AnMe3z/quadruped-version-3/encoder/encoder-wheels/encoder-wheel.FCStd

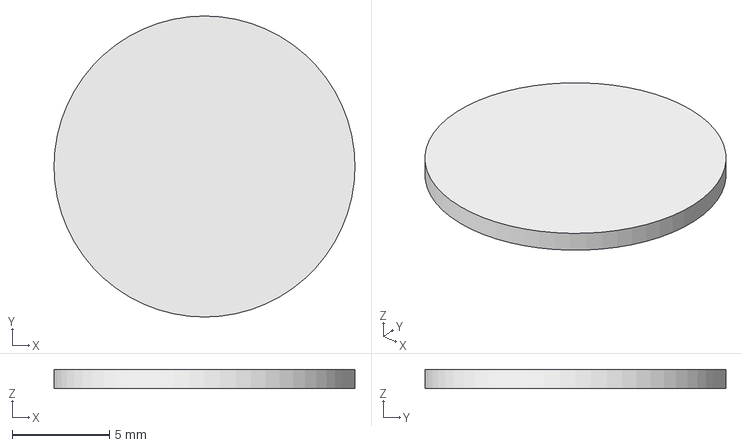
[picture p12: CAD file, 2023-12-13]
encoder/encoder-wheels/encoder-wheel.FCStd
15.5 x 15.5 x 1.00 mm
