AnMe3z/quadruped-version-3/encoder/gears/encoder-gear-Body.stl

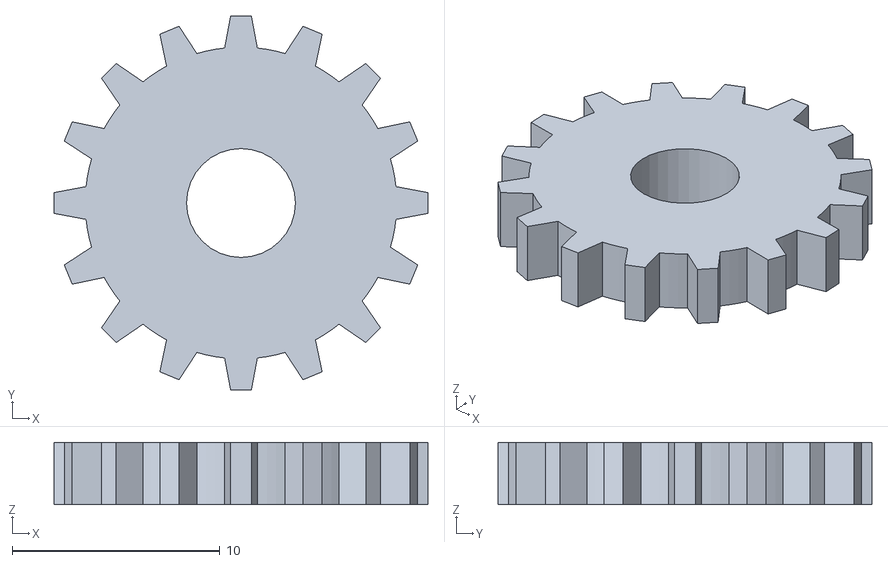
[picture p13: CAD file, 2023-12-22]
encoder/gears/encoder-gear-Body.stl
18.0 x 18.0 x 3.00
