AnMe3z/quadruped-version-3/encoder/sensor-base.FCStd

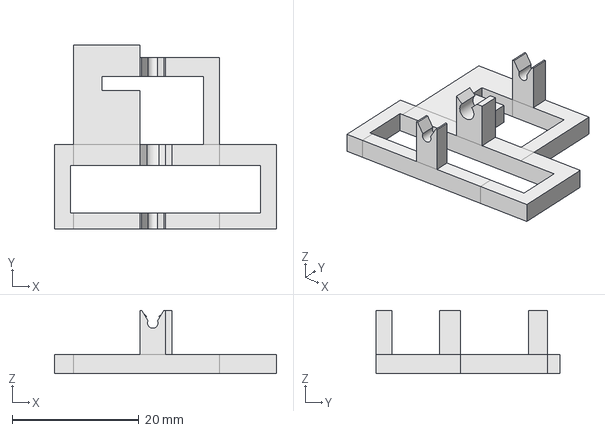
[picture p14: CAD file, 2023-12-06]
encoder/sensor-base.FCStd
35.0 x 29.0 x 10.0 mm
