AnMe3z/quadruped-version-3/encoder/wingEncoder/wing.FCStd

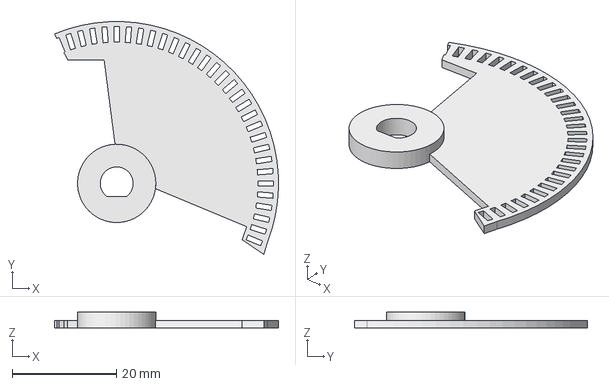
[picture p15: CAD file, 2023-12-23]
encoder/wingEncoder/wing.FCStd
42.9 x 44.6 x 3.00 mm
