AnMe3z/quadruped-version-3/hardware/body/parallel.FCStd

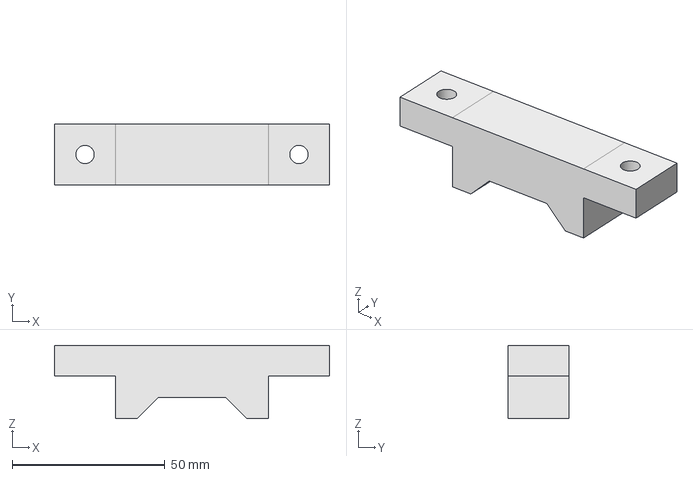
[picture p16: CAD file, 2024-03-18]
hardware/body/parallel.FCStd
90.0 x 20.0 x 24.0 mm
