AnMe3z/quadruped-version-3/hardware/leg/femur/femur-fragmented/femur-left.FCStd

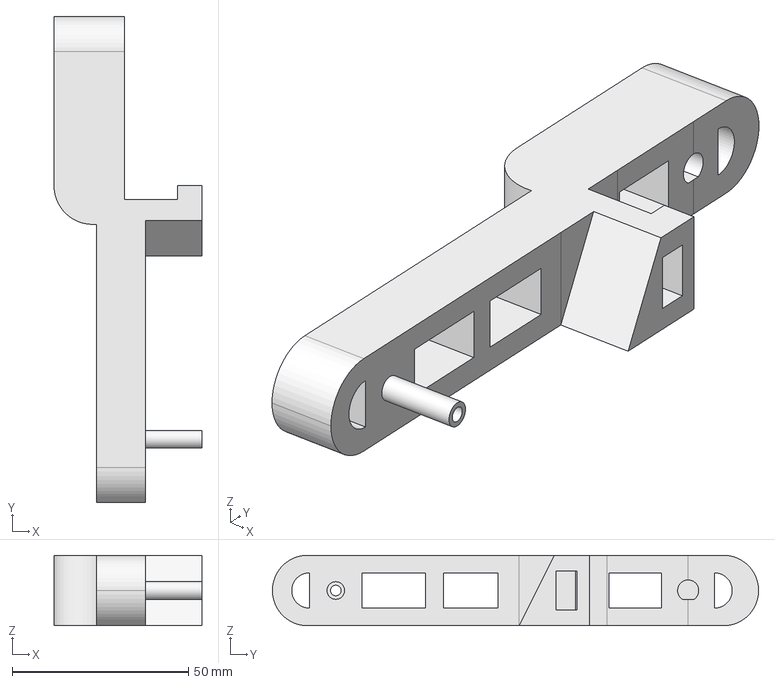
[picture p17: CAD file, 2023-12-28]
hardware/leg/femur/femur-fragmented/femur-left.FCStd
42.0 x 138.0 x 20.0 mm
