AnMe3z/quadruped-version-3/hardware/leg/femur/femur-inner.FCStd

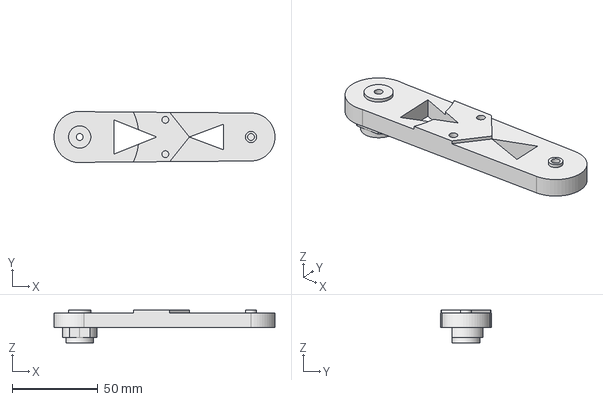
[picture p18: CAD file, 2024-04-03]
hardware/leg/femur/femur-inner.FCStd
129.0 x 30.0 x 19.0 mm
