AnMe3z/quadruped-version-3/hardware/leg/femur/tensioners/btens14.stl

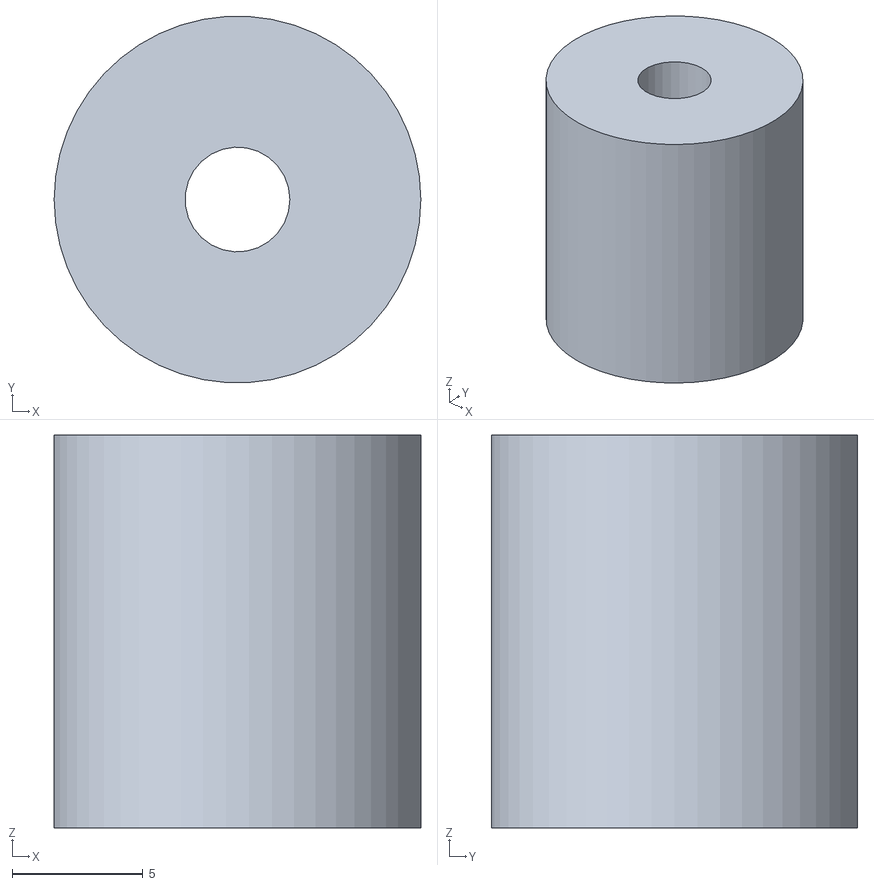
[picture p19: CAD file, 2024-01-30]
hardware/leg/femur/tensioners/btens14.stl
14.0 x 14.0 x 15.0
