AnMe3z/quadruped-version-3/hardware/leg/gears/Pulley_GT2-2MM-40T-11SH.stl

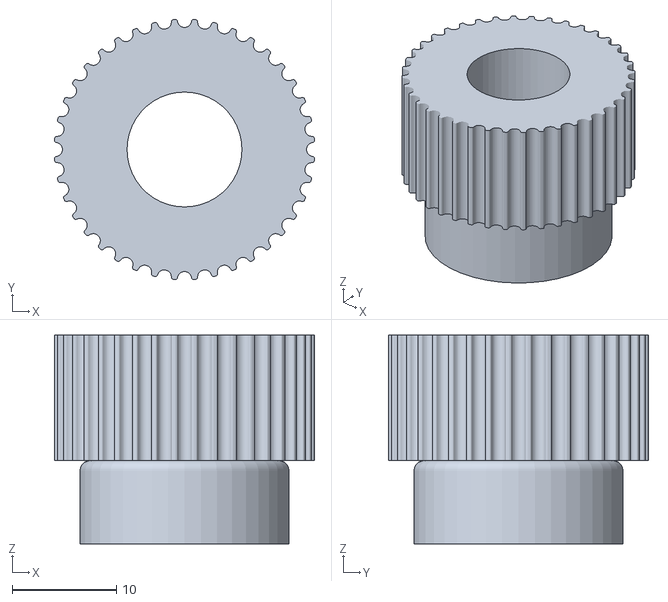
[picture p20: CAD file, 2024-02-03]
hardware/leg/gears/Pulley_GT2-2MM-40T-11SH.stl
24.9 x 24.9 x 20.0
