AnMe3z/quadruped-version-3/hardware/leg/hip/hip-lower/hip-lower-BR.stl

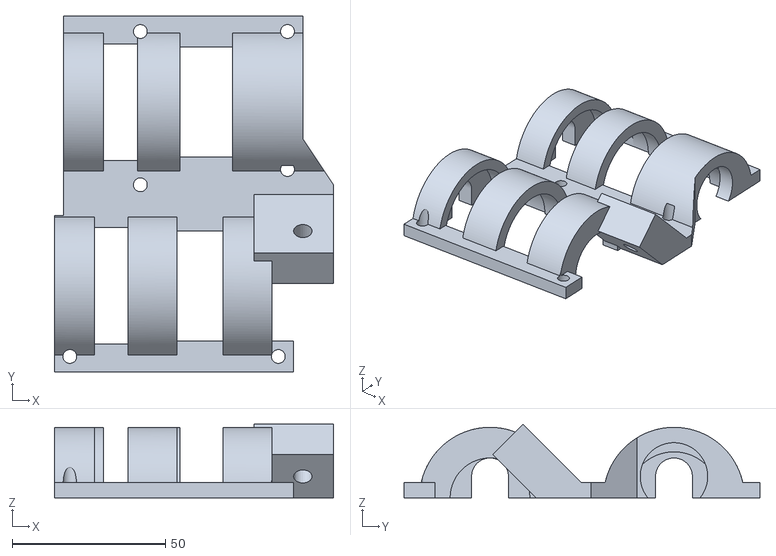
[picture p21: CAD file, 2024-02-26]
hardware/leg/hip/hip-lower/hip-lower-BR.stl
91.0 x 116.0 x 24.0
