AnMe3z/quadruped-version-3/hardware/leg/hip/hip-sensor-cap/hip-encoder-shell-long-proper-mirror.stl

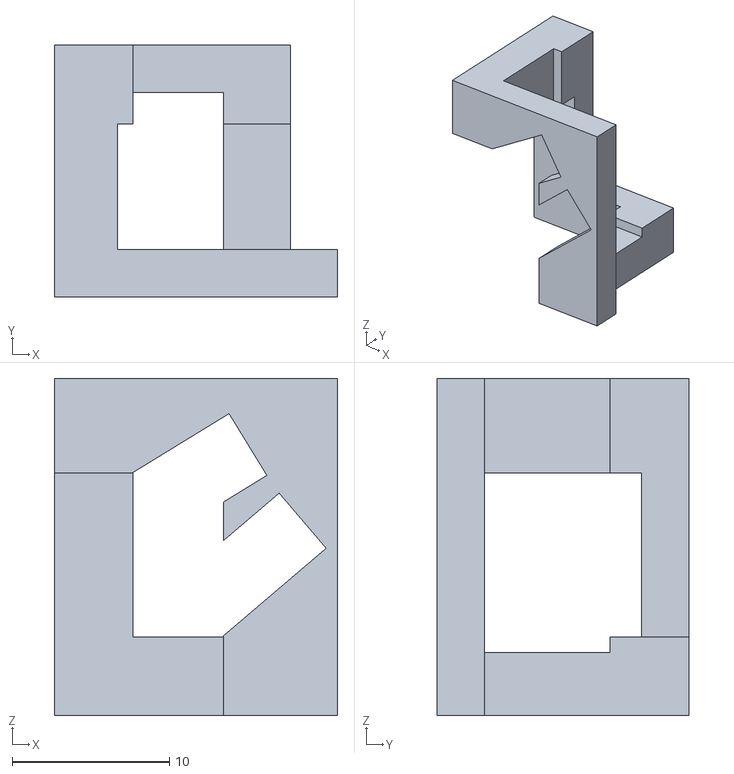
[picture p22: CAD file, 2024-04-03]
hardware/leg/hip/hip-sensor-cap/hip-encoder-shell-long-proper-mirror.stl
18.0 x 16.0 x 21.4
