AnMe3z/quadruped-version-3/hardware/leg/hip/hip-upper/hip-upper-BL.stl

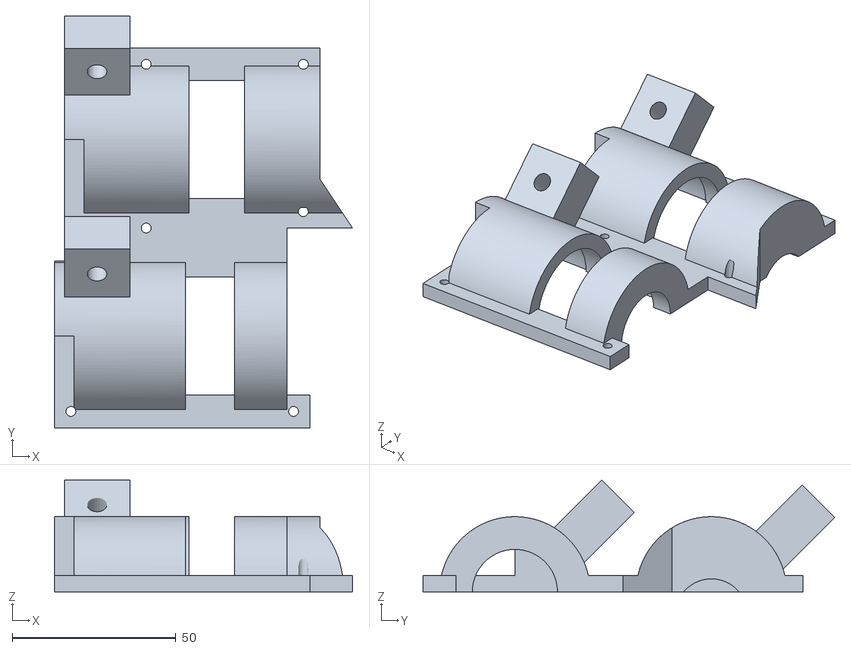
[picture p23: CAD file, 2024-02-26]
hardware/leg/hip/hip-upper/hip-upper-BL.stl
91.0 x 125.7 x 34.2
