AnMe3z/quadruped-version-3/hardware/leg/knee/cuts/61.stl

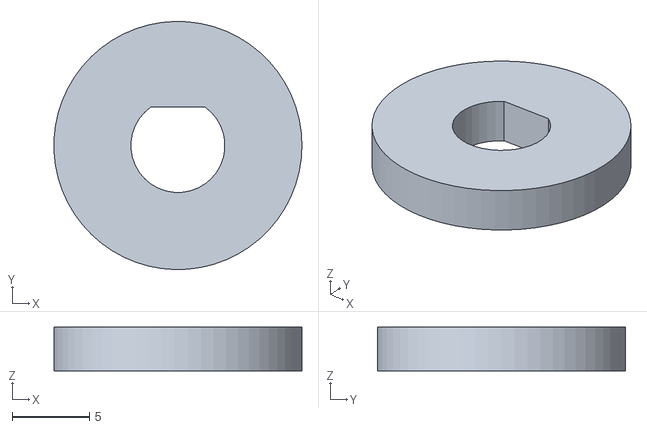
[picture p24: CAD file, 2024-04-03]
hardware/leg/knee/cuts/61.stl
16.1 x 16.1 x 2.83
