AnMe3z/quadruped-version-3/hardware/leg/knee/knee-drive.FCStd

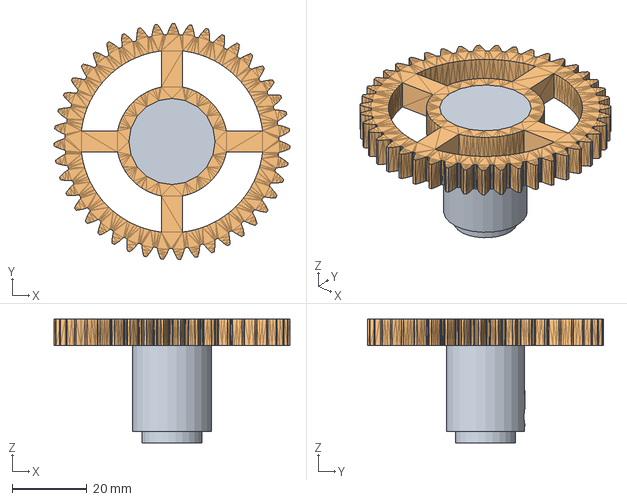
[picture p25: CAD file, 2024-04-03]
hardware/leg/knee/knee-drive.FCStd
63.0 x 63.0 x 33.0 mm
Stunning_Amberis__1_001 (Solid)
