AnMe3z/quadruped-version-3/hardware/leg/knee/knee-fragmented/knee-left.FCStd

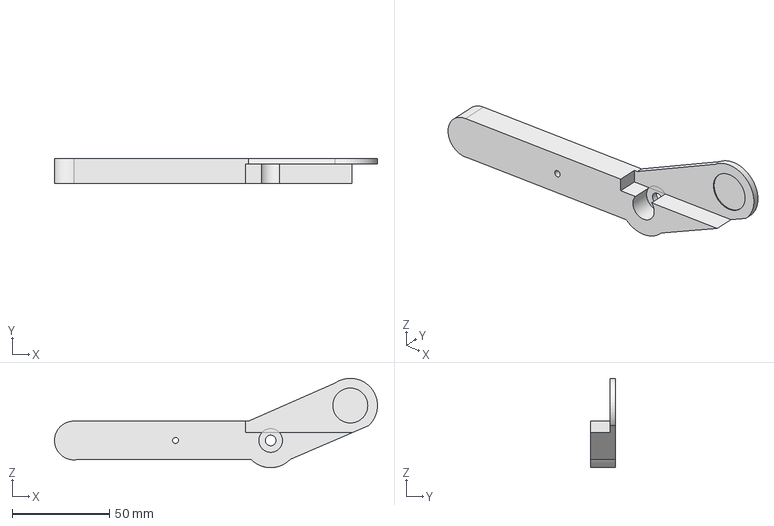
[picture p26: CAD file, 2023-12-28]
hardware/leg/knee/knee-fragmented/knee-left.FCStd
166.3 x 13.0 x 46.0 mm
