AnMe3z/quadruped-version-3/hardware/leg/leg-45.stl

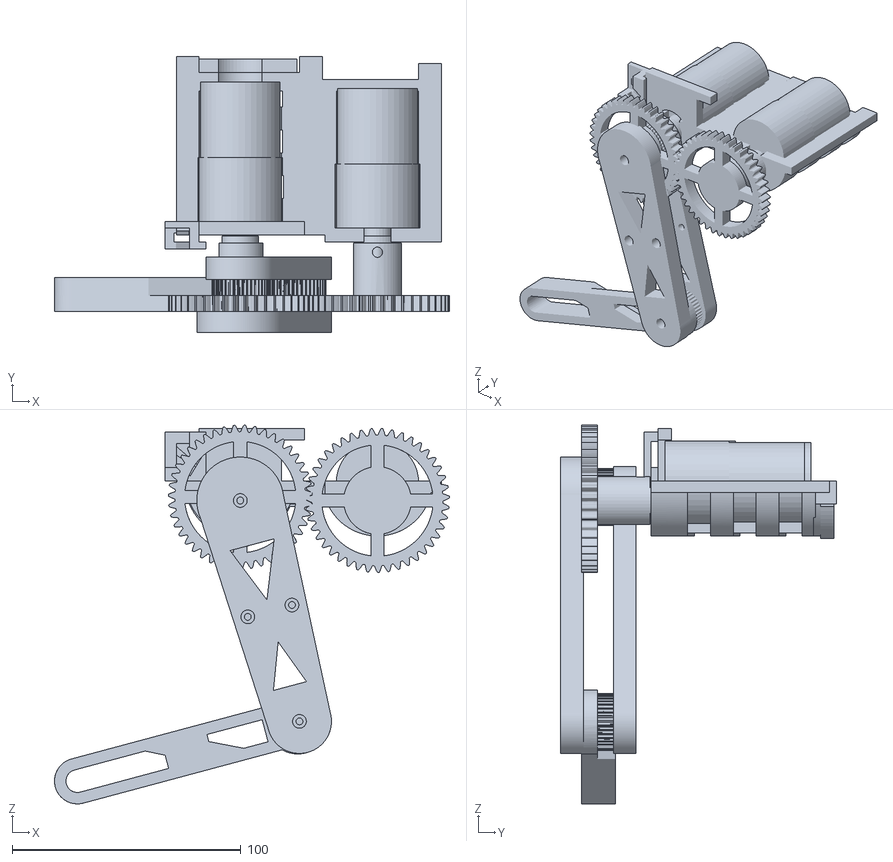
[picture p27: CAD file, 2024-02-03]
hardware/leg/leg-45.stl
172.7 x 120.5 x 165.7
