AnMe3z/quadruped-version-3/hardware/motor/test-fitting.FCStd

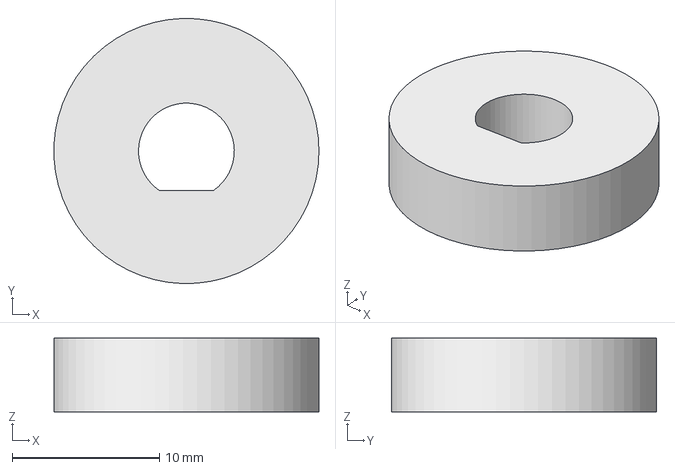
[picture p28: CAD file, 2024-01-26]
hardware/motor/test-fitting.FCStd
18.0 x 18.0 x 5.00 mm
