AnMe3z/quadruped-version-3/hardware/schematics/parts/3d-models/raspberry-pi-pico-w-rp2040-no-pins-pins-and-socketed-1.snapshot.5/RaspberryPi-PicoW-NoPins.step

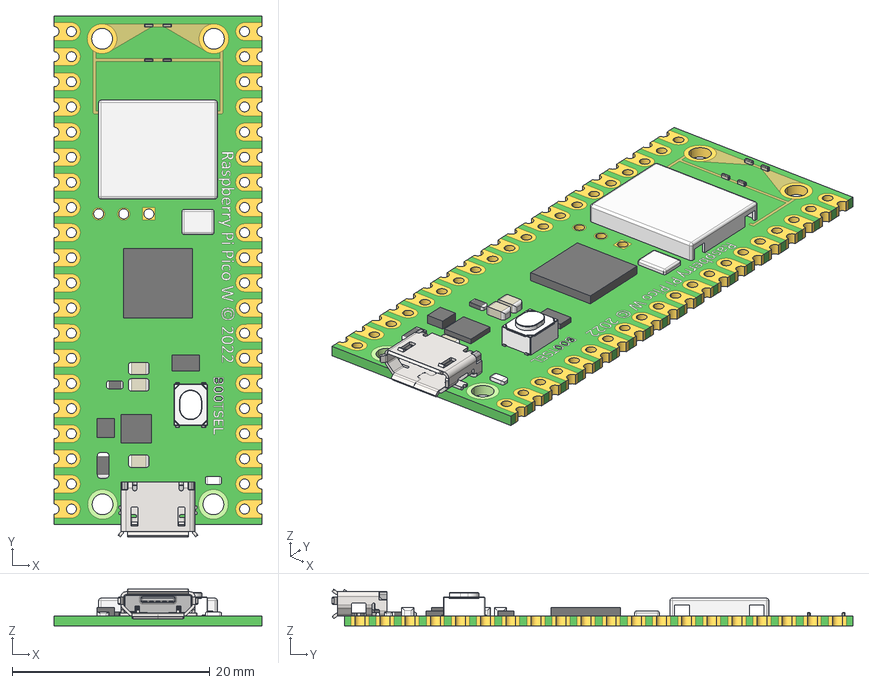
[picture p29: CAD file, 2024-02-05]
hardware/schematics/parts/3d-models/raspberry-pi-pico-w-rp2040-no-pins-pins-and-socketed-1.snapshot.5/RaspberryPi-PicoW-NoPins.step
21.0 x 52.7 x 3.71 mm
