AnMe3z/quadruped-version-3/hip/knee-drive.FCStd

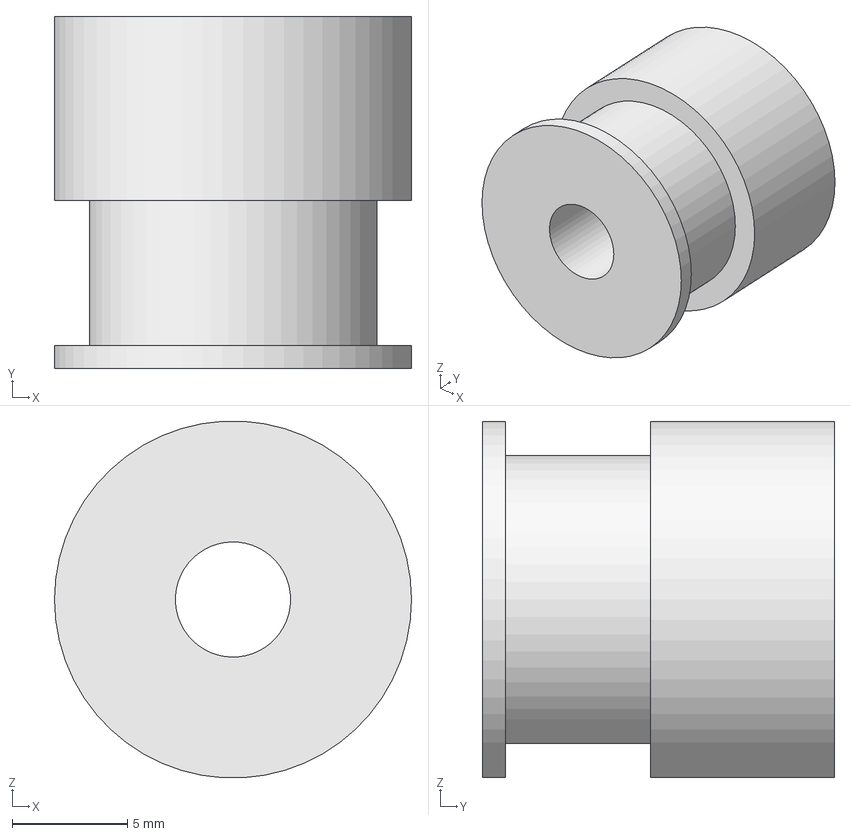
[picture p30: CAD file, 2023-10-18]
hip/knee-drive.FCStd
15.5 x 15.3 x 15.5 mm
