AnMe3z/quadruped-version-3/knee/knee-belt-drive-realistic.FCStd

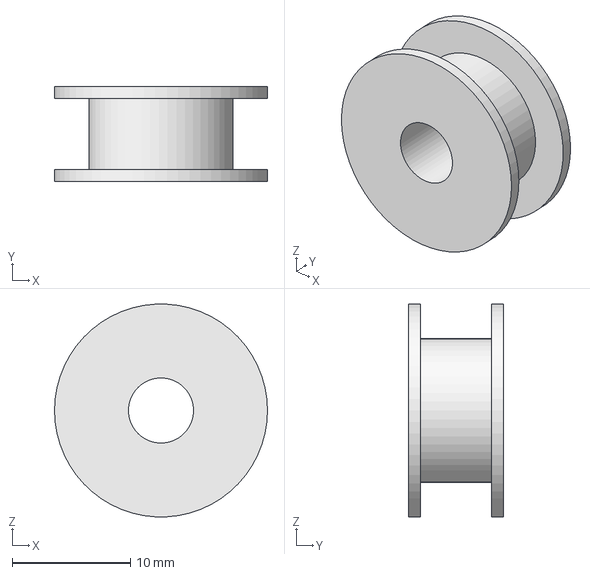
[picture p31: CAD file, 2023-10-26]
knee/knee-belt-drive-realistic.FCStd
18.0 x 8.00 x 18.0 mm
