AnMe3z/quadruped-version-3/encoder/wingEncoder/ledCover.FCStd

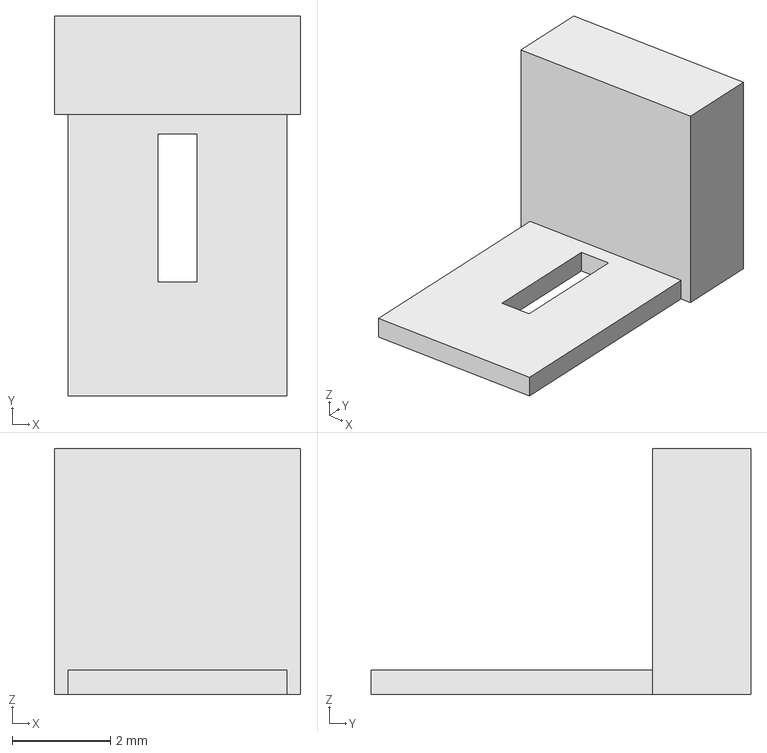
[picture p33: CAD file, 2023-12-22]
encoder/wingEncoder/ledCover.FCStd
5.00 x 7.72 x 5.00 mm
