AnMe3z/quadruped-version-3/hardware/body/side-lower-back.stl

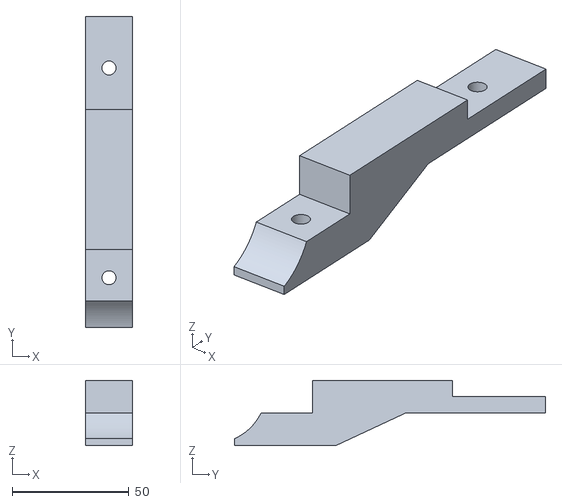
[picture p34: CAD file, 2024-03-18]
hardware/body/side-lower-back.stl
20.0 x 133.4 x 28.0
