AnMe3z/quadruped-version-3/hardware/leg/femur/tensioners/btens10.FCStd

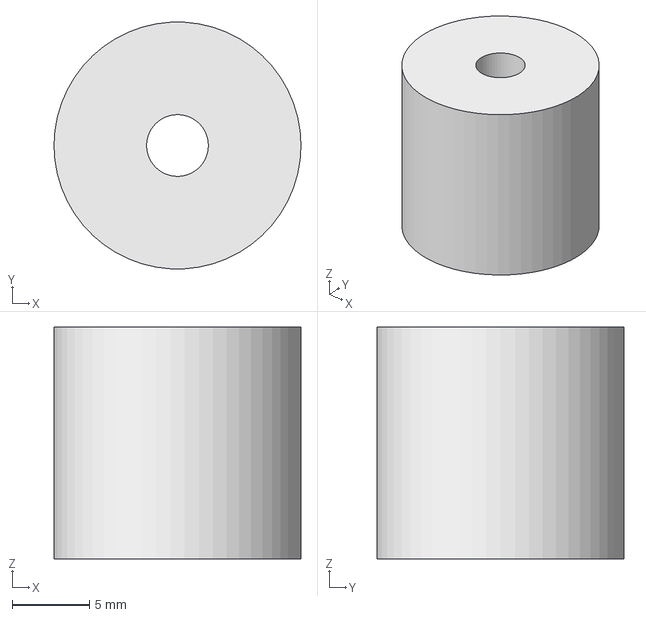
[picture p35: CAD file, 2024-01-30]
hardware/leg/femur/tensioners/btens10.FCStd
16.0 x 16.0 x 15.0 mm
