AnMe3z/quadruped-version-3/hardware/leg/gears/belt-gear.stl

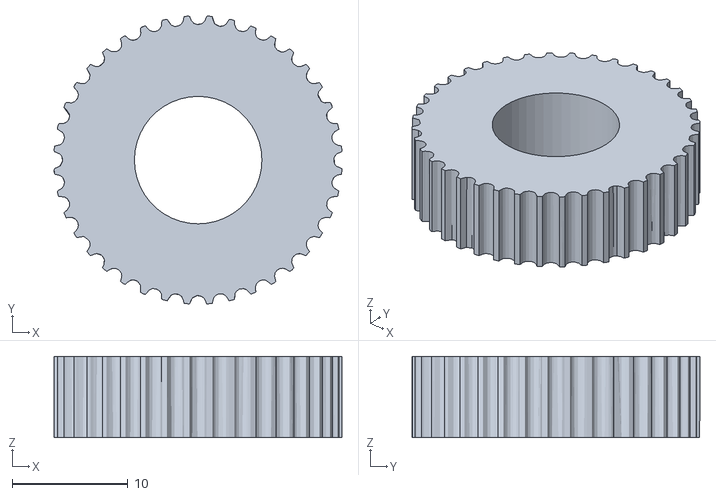
[picture p36: CAD file, 2024-02-03]
hardware/leg/gears/belt-gear.stl
24.9 x 24.8 x 7.00
