AnMe3z/quadruped-version-3/hardware/leg/hip/hip-sensor-cap/hip-sensor-cap.FCStd

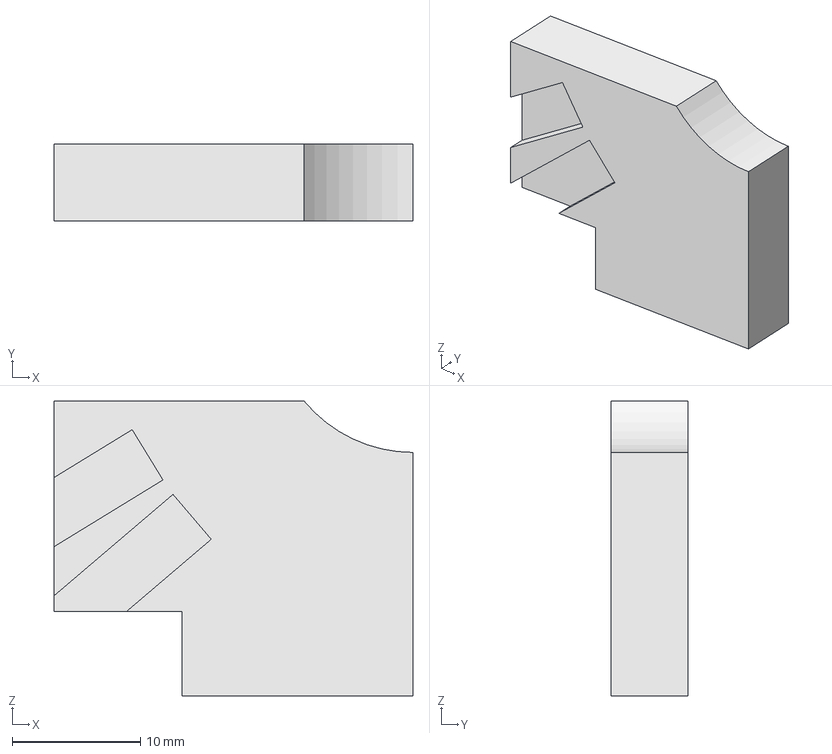
[picture p37: CAD file, 2024-03-18]
hardware/leg/hip/hip-sensor-cap/hip-sensor-cap.FCStd
28.0 x 6.00 x 23.0 mm
