AnMe3z/quadruped-version-3/hardware/leg/knee/knee-fragmented/knee-right.FCStd

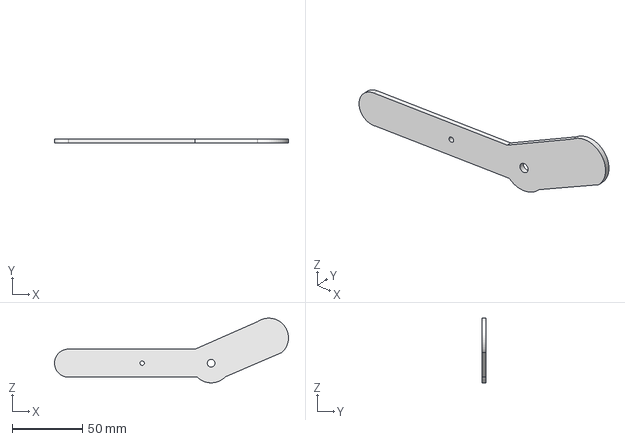
[picture p38: CAD file, 2023-12-28]
hardware/leg/knee/knee-fragmented/knee-right.FCStd
166.3 x 3.00 x 46.0 mm
