AnMe3z/quadruped-version-3/hardware/motor/xd-37gb520.FCStd

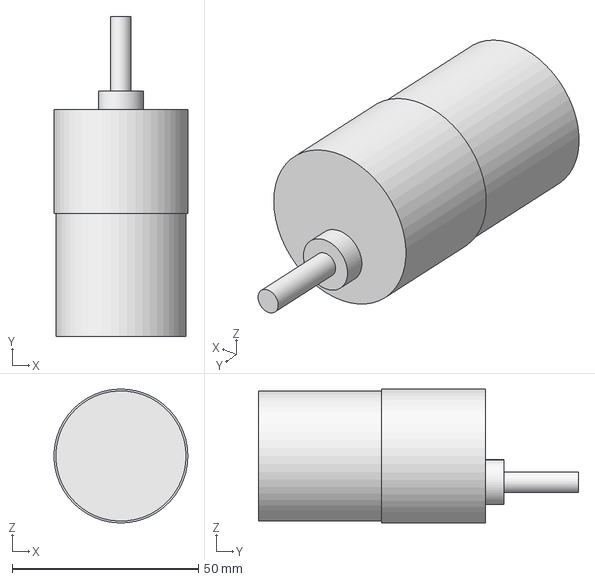
[picture p39: CAD file, 2023-10-10]
hardware/motor/xd-37gb520.FCStd
36.0 x 86.0 x 36.0 mm
