AnMe3z/quadruped-version-3/knee/knee-belt-drive.FCStd

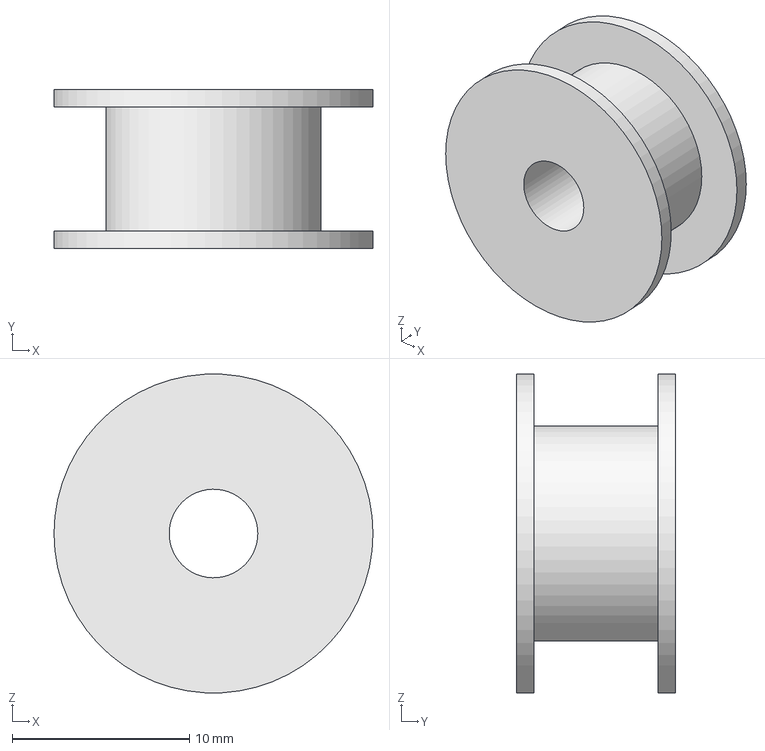
[picture p40: CAD file, 2023-10-18]
knee/knee-belt-drive.FCStd
18.0 x 9.00 x 18.0 mm
