AnMe3z/quadruped-version-3/encoder/gears/middle-gear-Body.stl

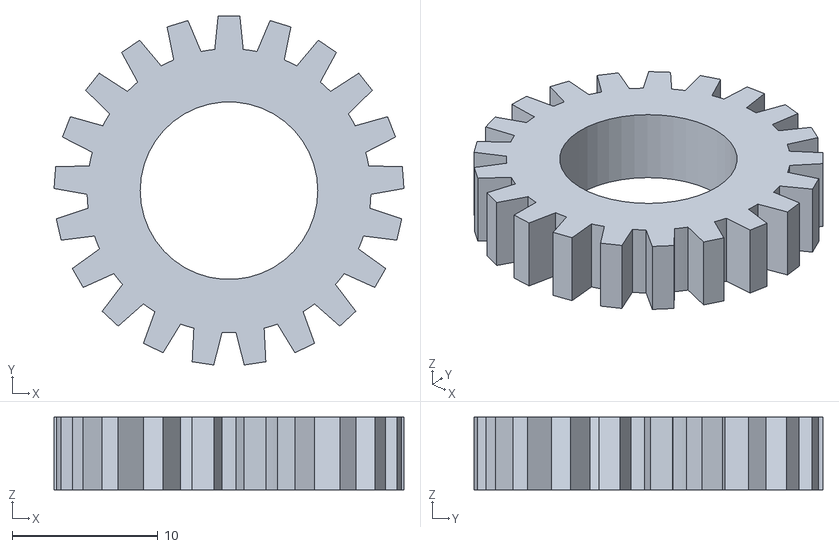
[picture p41: CAD file, 2023-12-17]
encoder/gears/middle-gear-Body.stl
24.0 x 24.0 x 5.00
