AnMe3z/quadruped-version-3/hardware/body/side-lower-front.stl

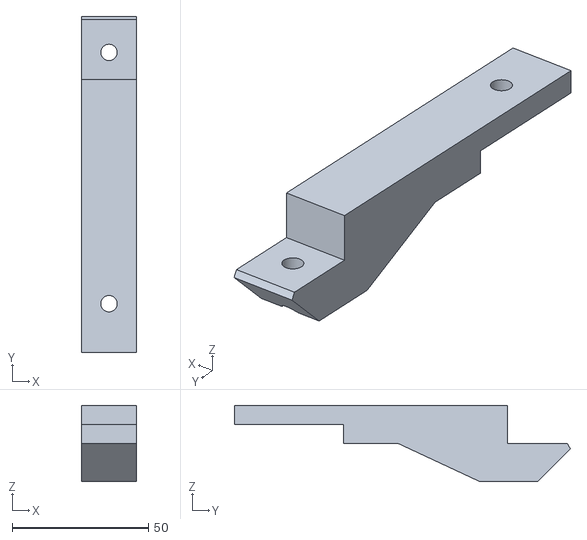
[picture p42: CAD file, 2024-03-18]
hardware/body/side-lower-front.stl
20.0 x 123.2 x 28.0
