AnMe3z/quadruped-version-3/hardware/leg/femur/femur-fragmented/femur-right.FCStd

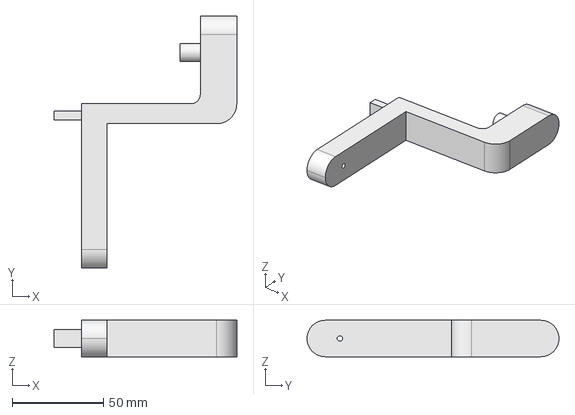
[picture p43: CAD file, 2023-10-26]
hardware/leg/femur/femur-fragmented/femur-right.FCStd
100.0 x 138.0 x 20.0 mm
