AnMe3z/quadruped-version-3/hardware/leg/femur/femur-outer-Body.stl

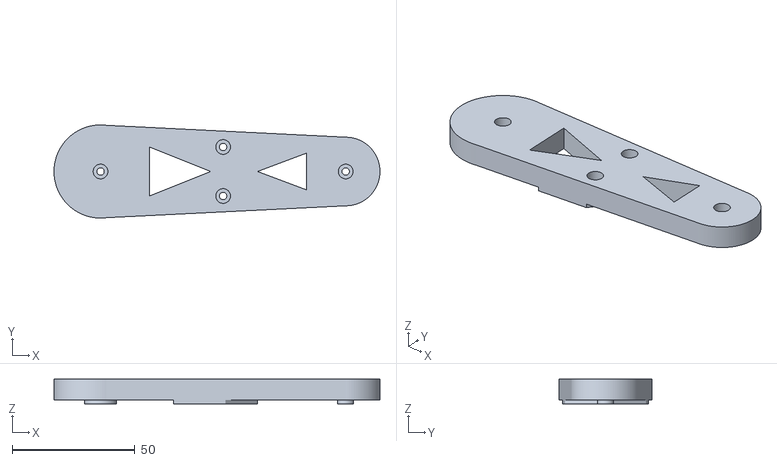
[picture p44: CAD file, 2024-02-03]
hardware/leg/femur/femur-outer-Body.stl
133.0 x 38.0 x 10.0
