AnMe3z/quadruped-version-3/hardware/leg/gears/gear667mm.stl

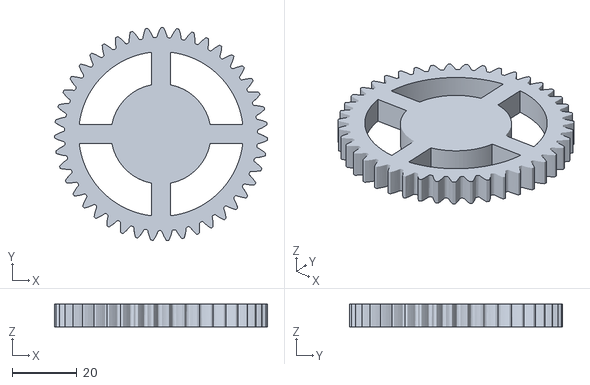
[picture p45: CAD file, 2024-01-27]
hardware/leg/gears/gear667mm.stl
66.0 x 66.0 x 7.00
