AnMe3z/quadruped-version-3/hardware/leg/leg-v1.FCStd

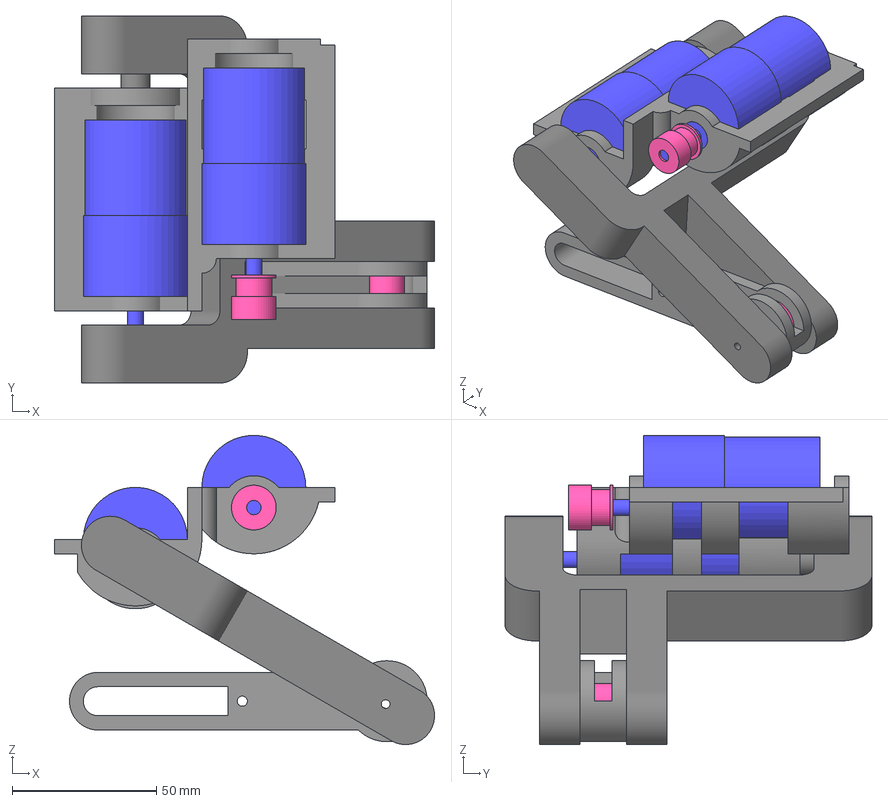
[picture p46: CAD file, 2024-01-30]
hardware/leg/leg-v1.FCStd
131.5 x 127.0 x 106.9 mm
hip-lower-Body
femur-xd-37gb520
knee-xd-37gb521
femur
knee-drive
knee
knee-belt-drive
