AnMe3z/quadruped-version-3/encoder/encoder-wheels/encoder-wheel-8-3mm.FCStd

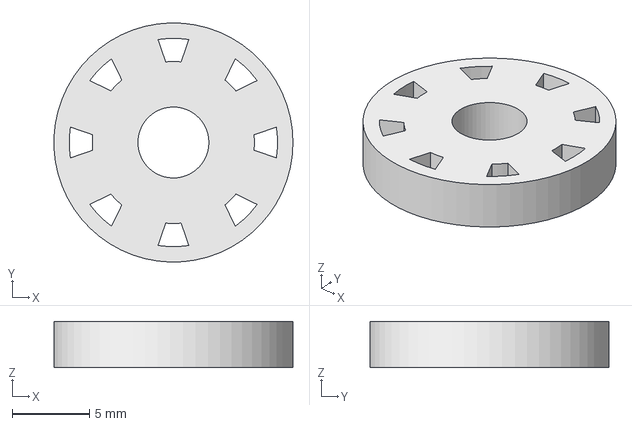
[picture p47: CAD file, 2023-12-13]
encoder/encoder-wheels/encoder-wheel-8-3mm.FCStd
15.5 x 15.5 x 3.00 mm
