AnMe3z/quadruped-version-3/hardware/leg/femur/femur-drive-gear.stl

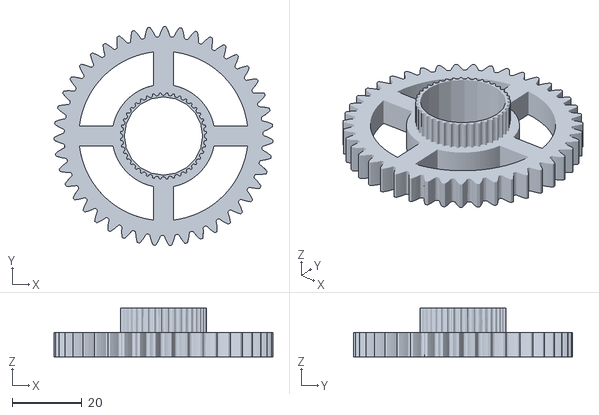
[picture p48: CAD file, 2024-02-03]
hardware/leg/femur/femur-drive-gear.stl
63.0 x 63.0 x 14.0
