AnMe3z/quadruped-version-3/hardware/leg/hip/hip-lower/hip-lower-front.FCStd

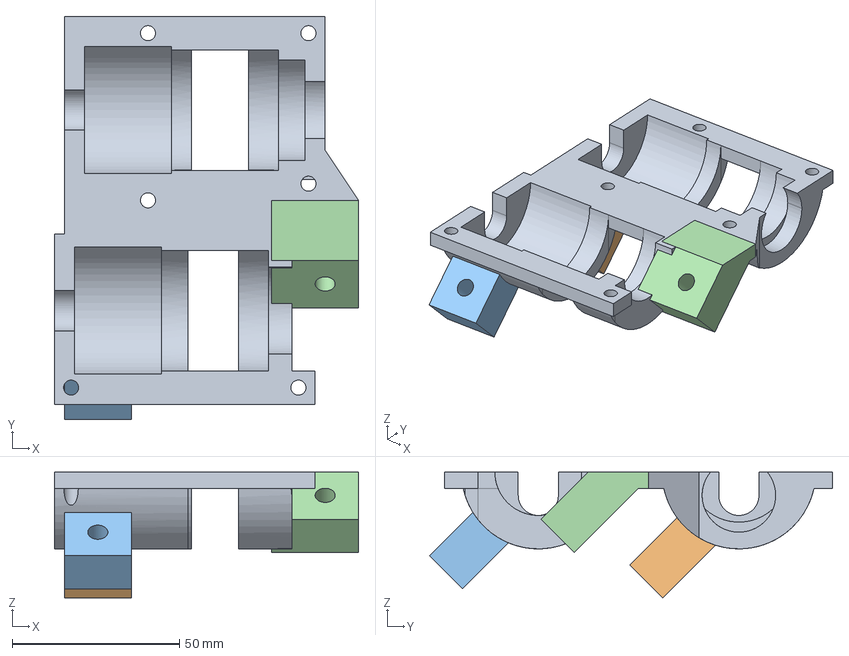
[picture p49: CAD file, 2024-02-26]
hardware/leg/hip/hip-lower/hip-lower-front.FCStd
91.0 x 120.5 x 37.7 mm
