AnMe3z/quadruped-version-3/hardware/leg/hip/hip-upper/hip-upper-front.FCStd

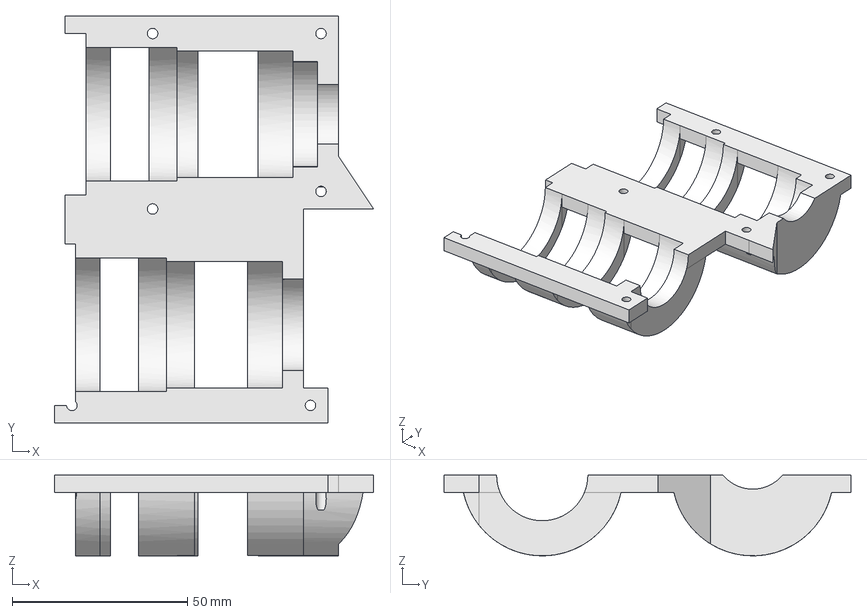
[picture p50: CAD file, 2024-02-26]
hardware/leg/hip/hip-upper/hip-upper-front.FCStd
91.0 x 116.0 x 23.0 mm
