AnMe3z/quadruped-version-3/hardware/leg/knee/knee-with-gear.stl

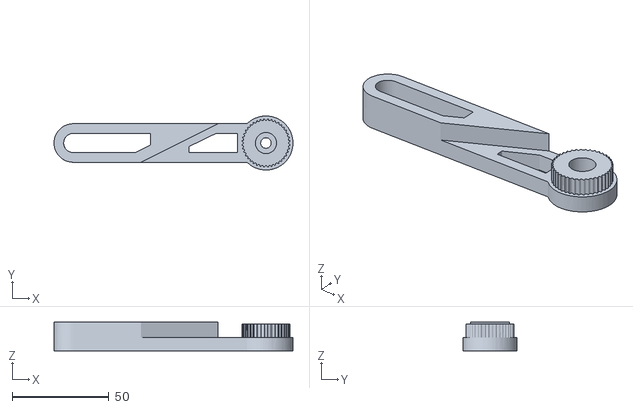
[picture p51: CAD file, 2024-02-03]
hardware/leg/knee/knee-with-gear.stl
123.8 x 28.0 x 15.0
