AnMe3z/quadruped-version-3/hardware/leg/leg.FCStd

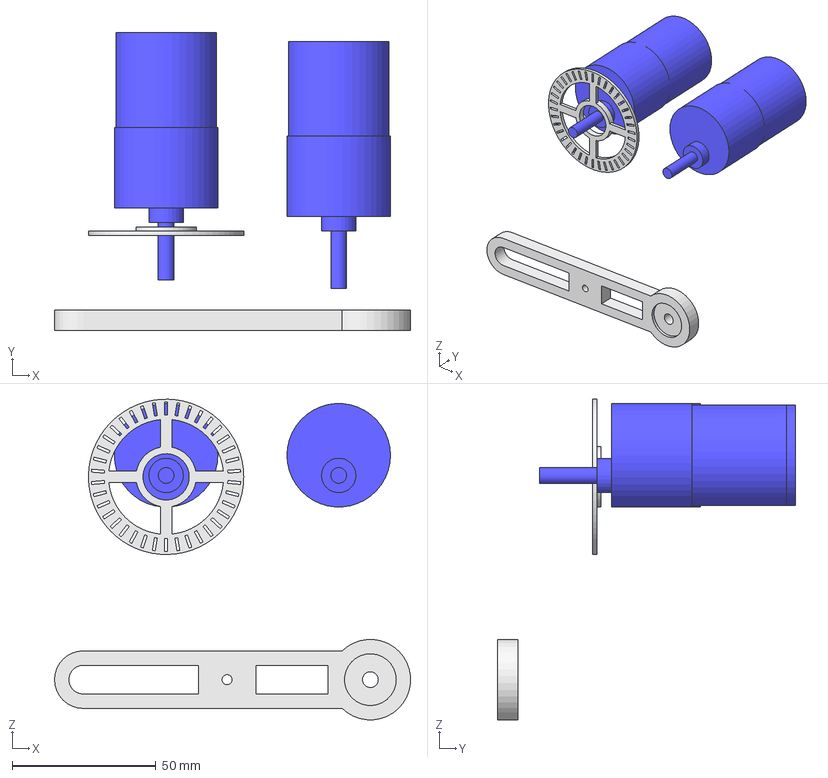
[picture p52: CAD file, 2024-01-30]
hardware/leg/leg.FCStd
123.7 x 103.5 x 111.4 mm
femur-xd-37gb520
knee-xd-37gb521
wingFullBelt38Cut001
knee-outer-Body
