AnMe3z/quadruped-version-3/encoder/gears/on-motor-gear-Body.stl

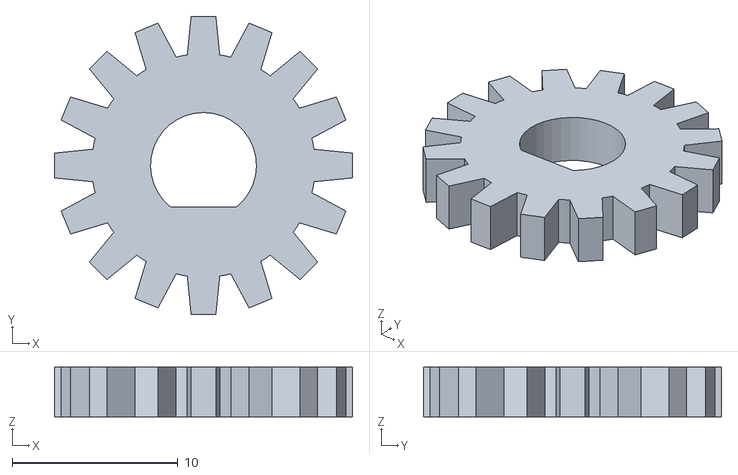
[picture p53: CAD file, 2023-12-17]
encoder/gears/on-motor-gear-Body.stl
18.0 x 18.0 x 3.00
