AnMe3z/quadruped-version-3/hardware/body/side-upper.FCStd

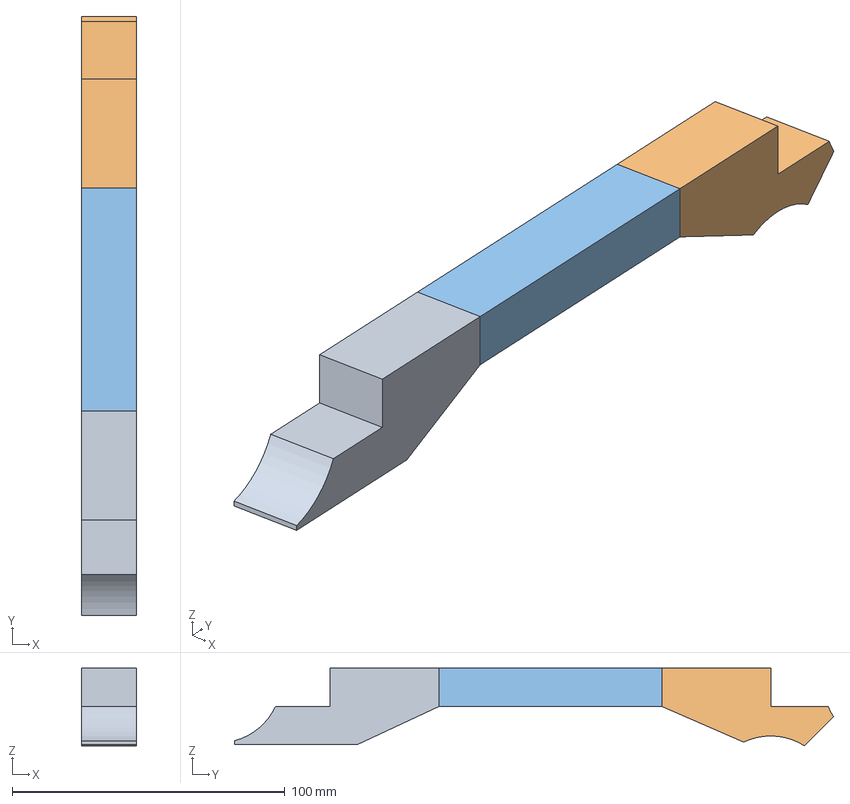
[picture p54: CAD file, 2024-02-18]
hardware/body/side-upper.FCStd
20.0 x 219.6 x 28.4 mm
Hip-lower
Hip-upper
