AnMe3z/quadruped-version-3/hardware/leg/knee/knee.FCStd

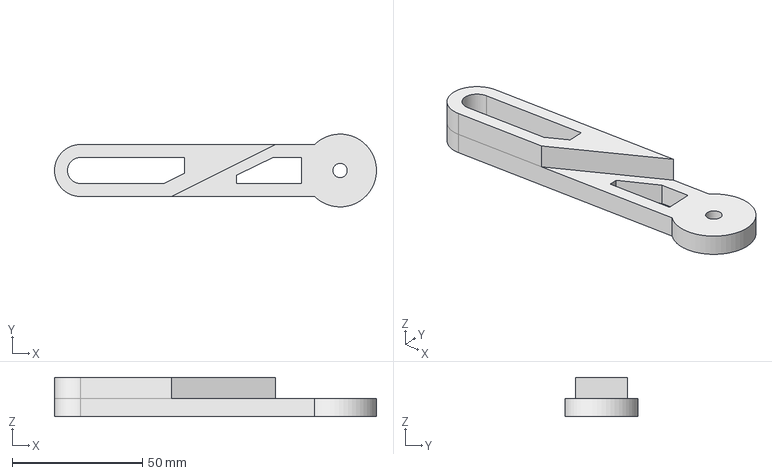
[picture p55: CAD file, 2024-02-03]
hardware/leg/knee/knee.FCStd
123.8 x 28.0 x 15.0 mm
