AnMe3z/quadruped-version-3/hardware/body/side.FCStd

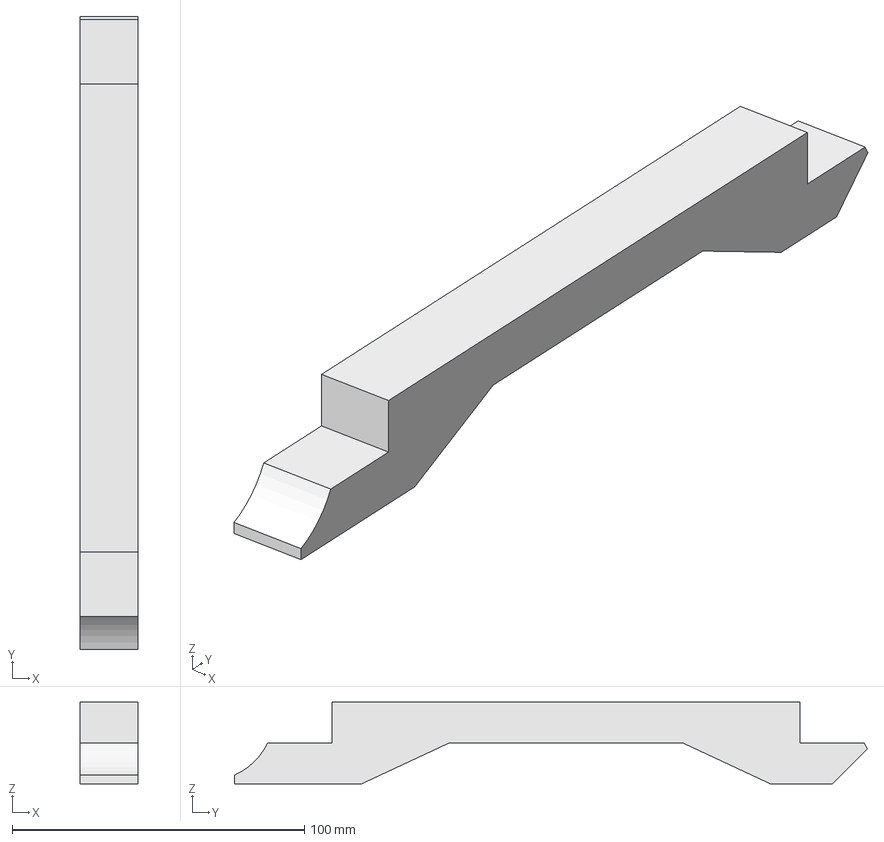
[picture p56: CAD file, 2024-02-18]
hardware/body/side.FCStd
20.0 x 216.6 x 28.0 mm
