AnMe3z/quadruped-version-3/hardware/leg/femur/belt-keep-ring.FCStd

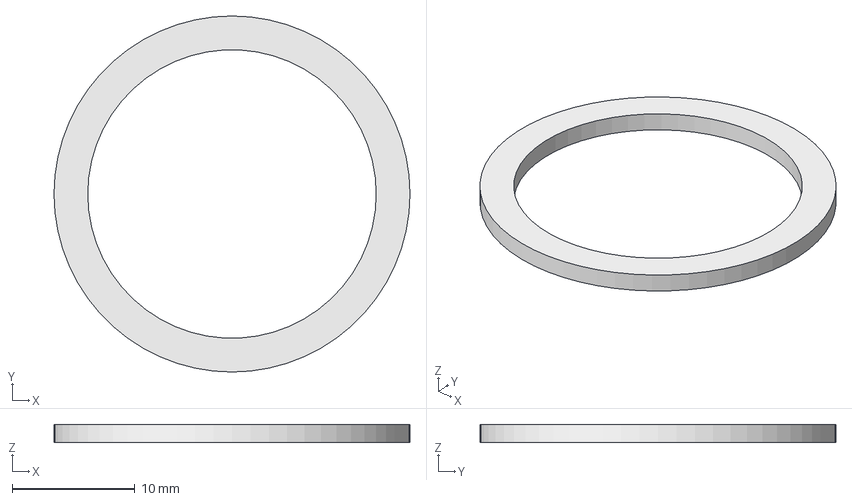
[picture p57: CAD file, 2024-02-03]
hardware/leg/femur/belt-keep-ring.FCStd
29.0 x 29.0 x 1.50 mm
