AnMe3z/quadruped-version-3/hardware/leg/hip/hip-sensor-cap/led-shield-ED.stl

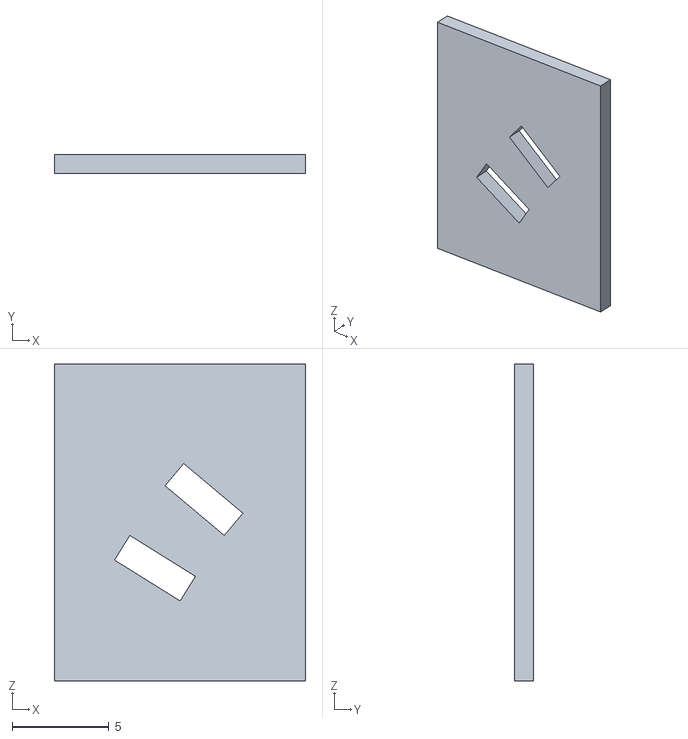
[picture p58: CAD file, 2024-02-04]
hardware/leg/hip/hip-sensor-cap/led-shield-ED.stl
13.0 x 1.00 x 16.4
