AnMe3z/quadruped-version-3/encoder/gears/mid-gear-arm-Body.stl

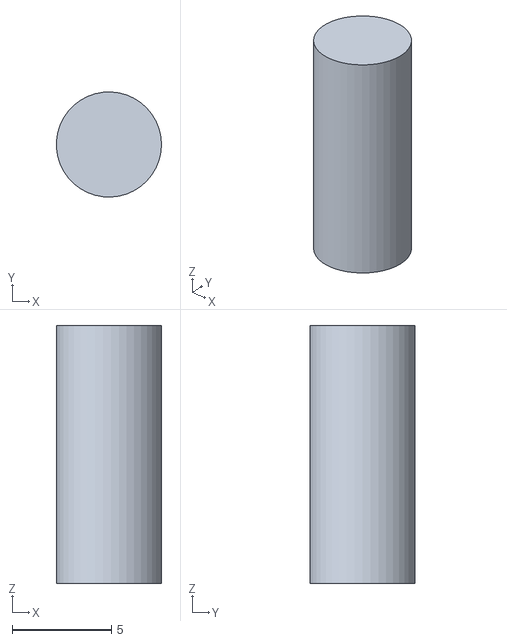
[picture p59: CAD file, 2023-12-13]
encoder/gears/mid-gear-arm-Body.stl
5.29 x 5.30 x 13.0
