AnMe3z/quadruped-version-3/hardware/leg/hip/hip-lower/hip-lower.FCStd

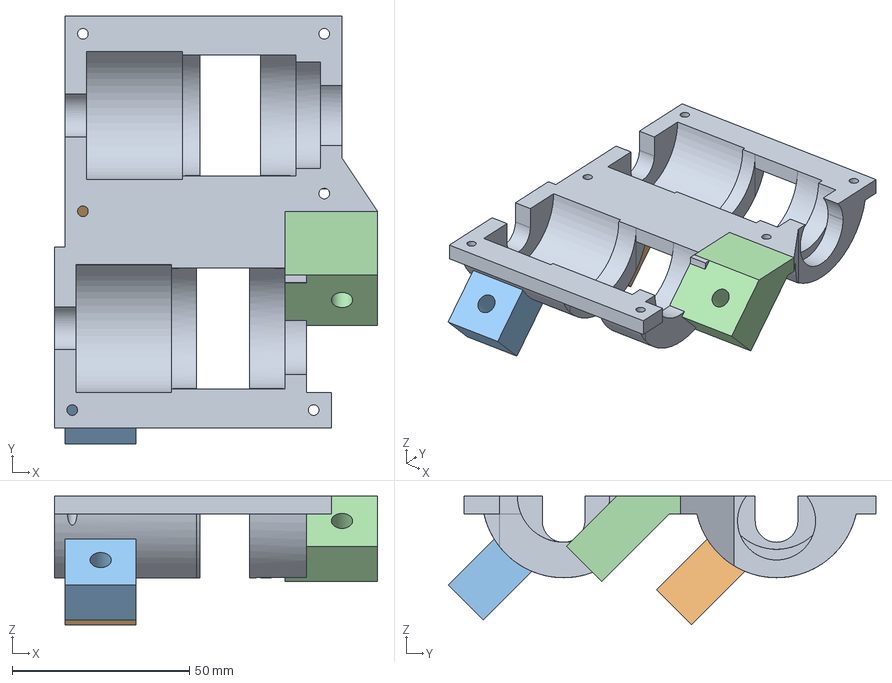
[picture p60: CAD file, 2024-02-17]
hardware/leg/hip/hip-lower/hip-lower.FCStd
91.0 x 120.5 x 36.3 mm
