AnMe3z/quadruped-version-3/hardware/leg/hip/hip-upper/hip-upper.FCStd

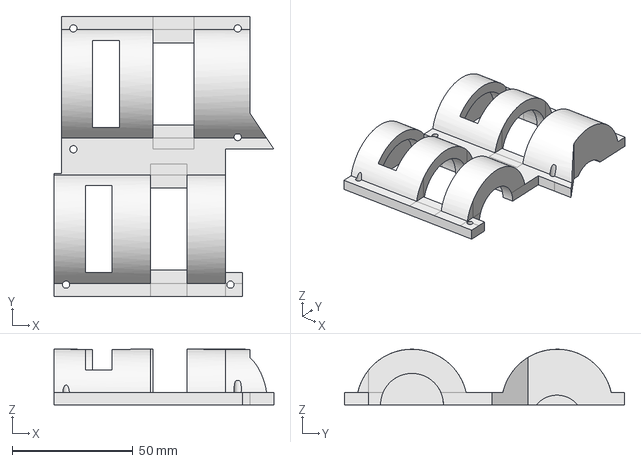
[picture p61: CAD file, 2024-02-17]
hardware/leg/hip/hip-upper/hip-upper.FCStd
91.0 x 116.0 x 23.0 mm
