AnMe3z/quadruped-version-3/hardware/leg/knee/knee-drive-final.stl

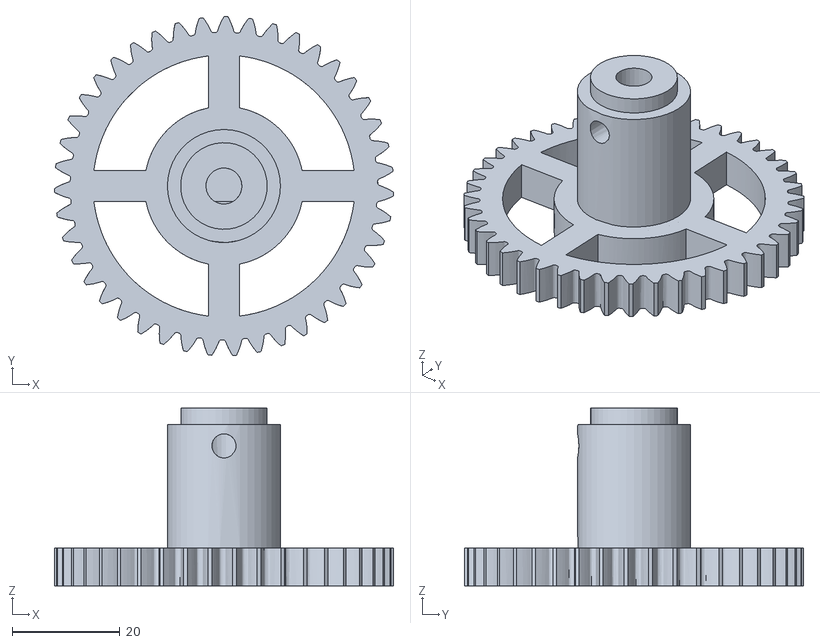
[picture p62: CAD file, 2024-01-30]
hardware/leg/knee/knee-drive-final.stl
63.0 x 63.0 x 33.0
