AnMe3z/quadruped-version-3/hardware/leg/encoder/wingEncoder/encoder_mask_wrong.dxf

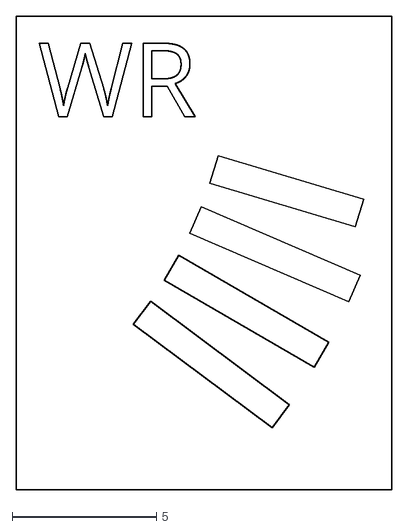
[picture p63: CAD file, 2024-02-17]
hardware/leg/encoder/wingEncoder/encoder_mask_wrong.dxf
13.0 x 16.4
