AnMe3z/quadruped-version-3/hardware/leg/femur/gear-pin.stl

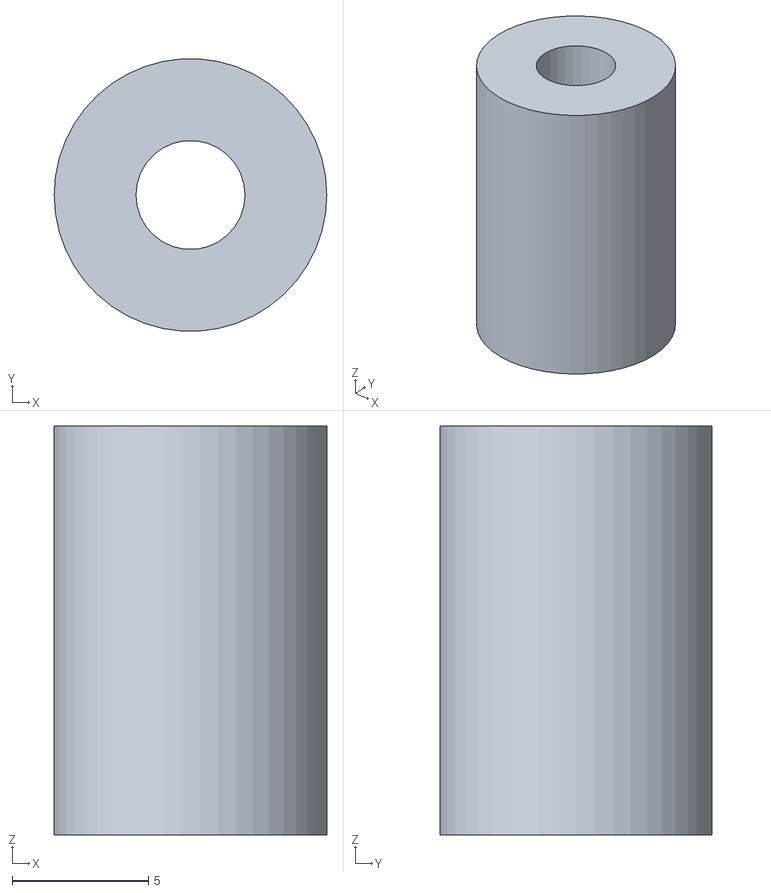
[picture p64: CAD file, 2024-02-02]
hardware/leg/femur/gear-pin.stl
10.0 x 9.98 x 15.0
