AnMe3z/quadruped-version-3/hardware/leg/hip/hip-lower/hip-lower-patch.FCStd

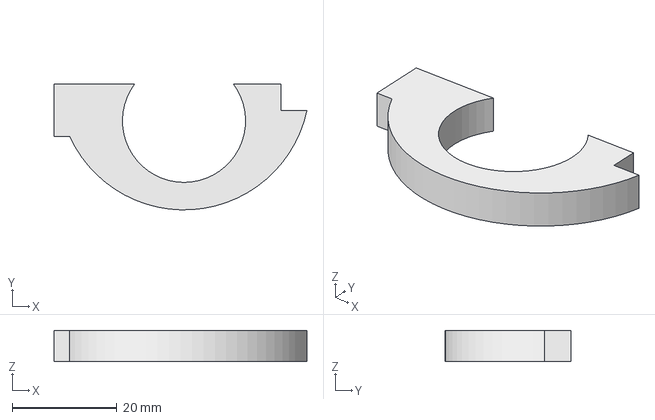
[picture p65: CAD file, 2024-01-02]
hardware/leg/hip/hip-lower/hip-lower-patch.FCStd
48.3 x 24.0 x 6.00 mm
