AnMe3z/quadruped-version-3/hardware/leg/hip/hip-sensor-cap/led-shield-DD.stl

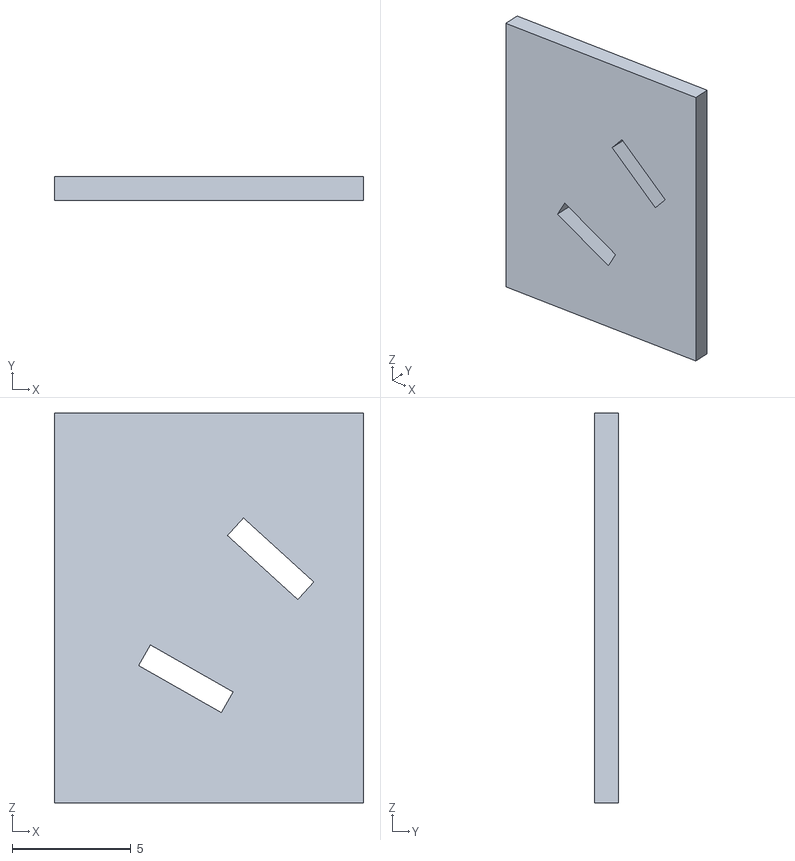
[picture p66: CAD file, 2024-02-03]
hardware/leg/hip/hip-sensor-cap/led-shield-DD.stl
13.0 x 1.00 x 16.4
