AnMe3z/quadruped-version-3/hardware/leg/encoder/wingEncoder/encoder_mask_proper.dxf

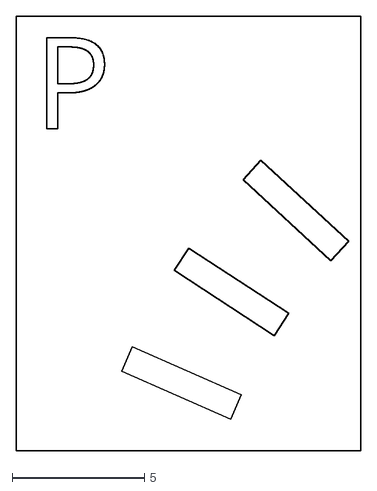
[picture p67: CAD file, 2024-02-17]
hardware/leg/encoder/wingEncoder/encoder_mask_proper.dxf
13.0 x 16.4
