AnMe3z/quadruped-version-3/hardware/leg/femur/belt-gear.FCStd

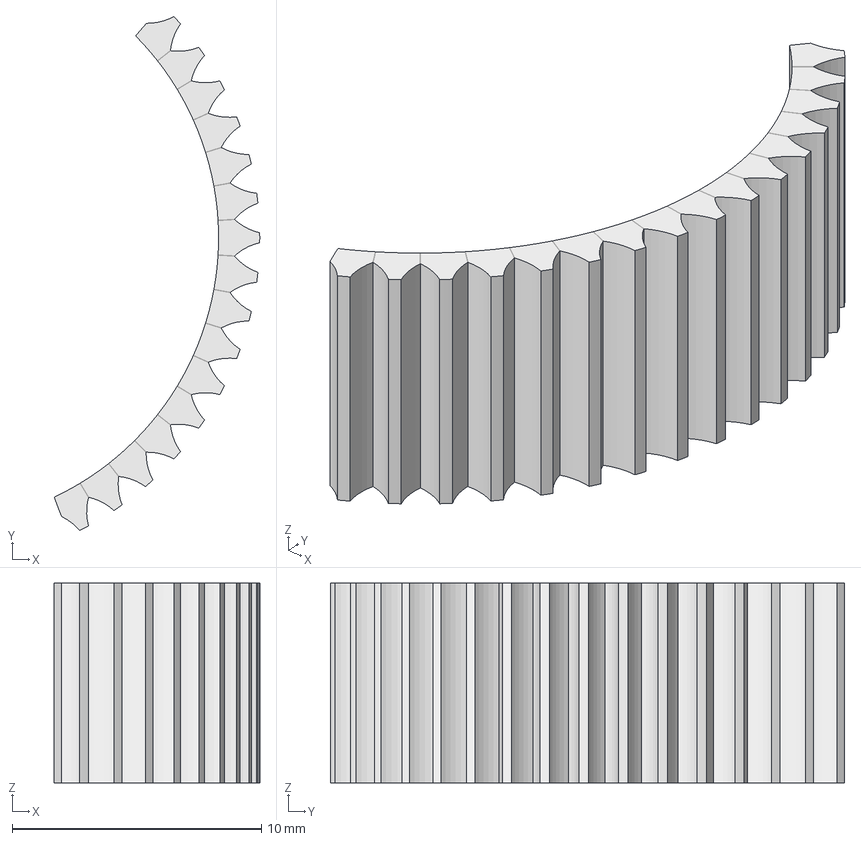
[picture p68: CAD file, 2024-02-02]
hardware/leg/femur/belt-gear.FCStd
8.24 x 20.6 x 8.00 mm
