AnMe3z/quadruped-version-3/hardware/leg/femur/femur-gear-double-pin.FCStd

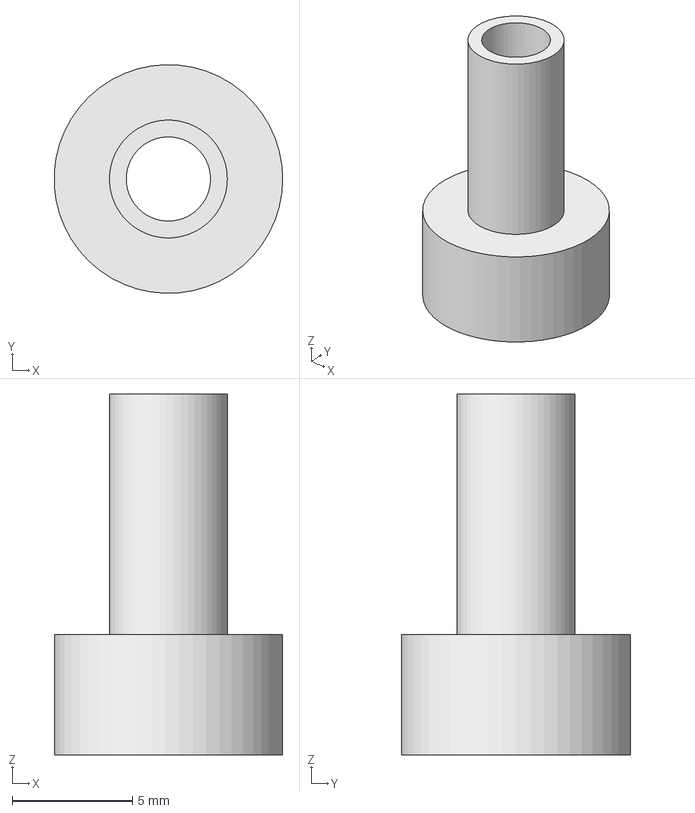
[picture p69: CAD file, 2024-01-30]
hardware/leg/femur/femur-gear-double-pin.FCStd
9.49 x 9.50 x 15.0 mm
