AnMe3z/quadruped-version-3/hardware/leg/hip/hip-lower/hip-lower-Body.stl

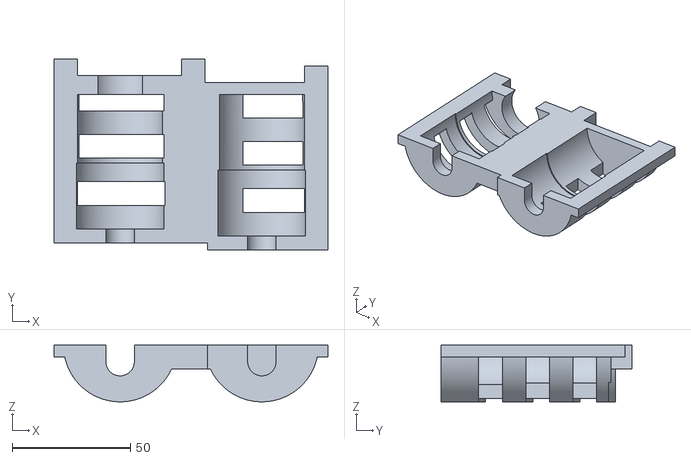
[picture p70: CAD file, 2023-12-28]
hardware/leg/hip/hip-lower/hip-lower-Body.stl
116.0 x 81.0 x 24.0
