AnMe3z/quadruped-version-3/hardware/leg/encoder/wingEncoder/wingCut.FCStd

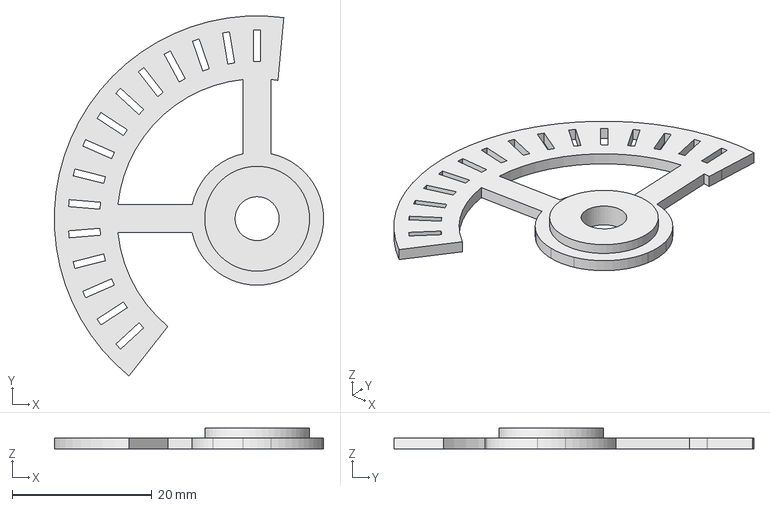
[picture p71: CAD file, 2024-01-21]
hardware/leg/encoder/wingEncoder/wingCut.FCStd
38.5 x 51.5 x 3.00 mm
