AnMe3z/quadruped-version-3/hardware/leg/femur/drive-ring-Body.stl

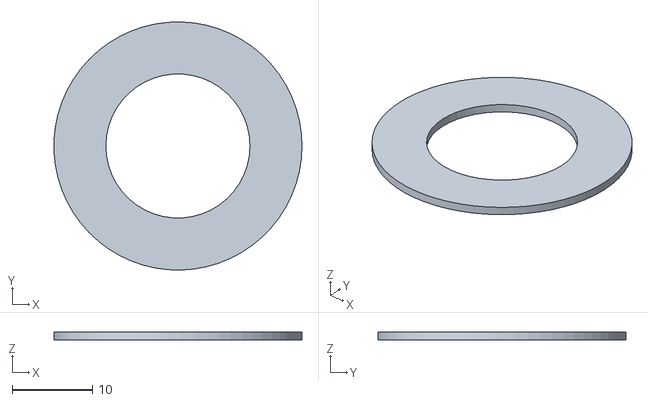
[picture p72: CAD file, 2024-01-29]
hardware/leg/femur/drive-ring-Body.stl
31.0 x 31.0 x 1.00
