AnMe3z/quadruped-version-3/hardware/leg/hip/hip-sensor-cap/led-shield-AA.stl

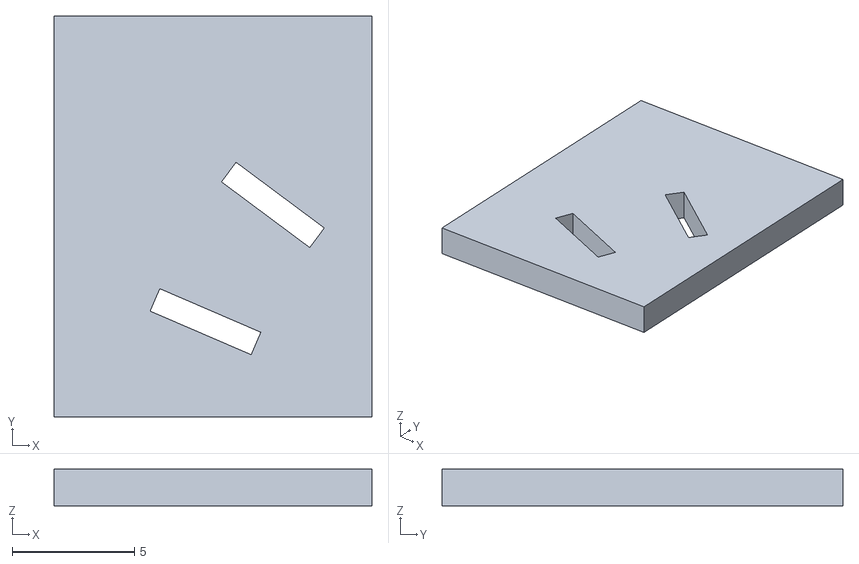
[picture p73: CAD file, 2024-02-03]
hardware/leg/hip/hip-sensor-cap/led-shield-AA.stl
13.0 x 16.4 x 1.50
