AnMe3z/quadruped-version-3/hardware/leg/hip/hip-sensor-cap/led-shield-CA.stl

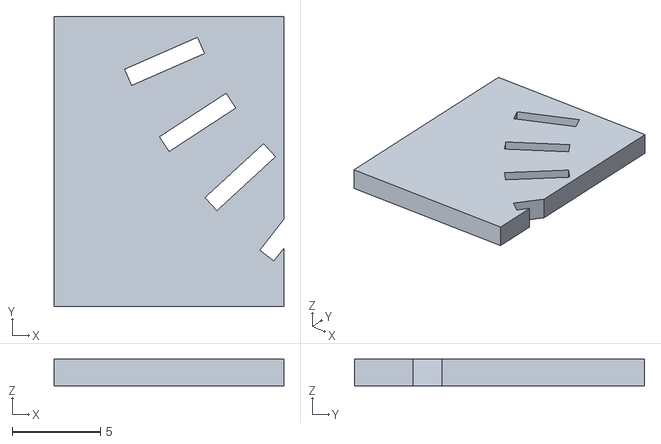
[picture p74: CAD file, 2024-02-03]
hardware/leg/hip/hip-sensor-cap/led-shield-CA.stl
13.0 x 16.4 x 1.50
