AnMe3z/quadruped-version-3/hardware/leg/hip/hip-sensor-cap/hip-encoder-shell.stl

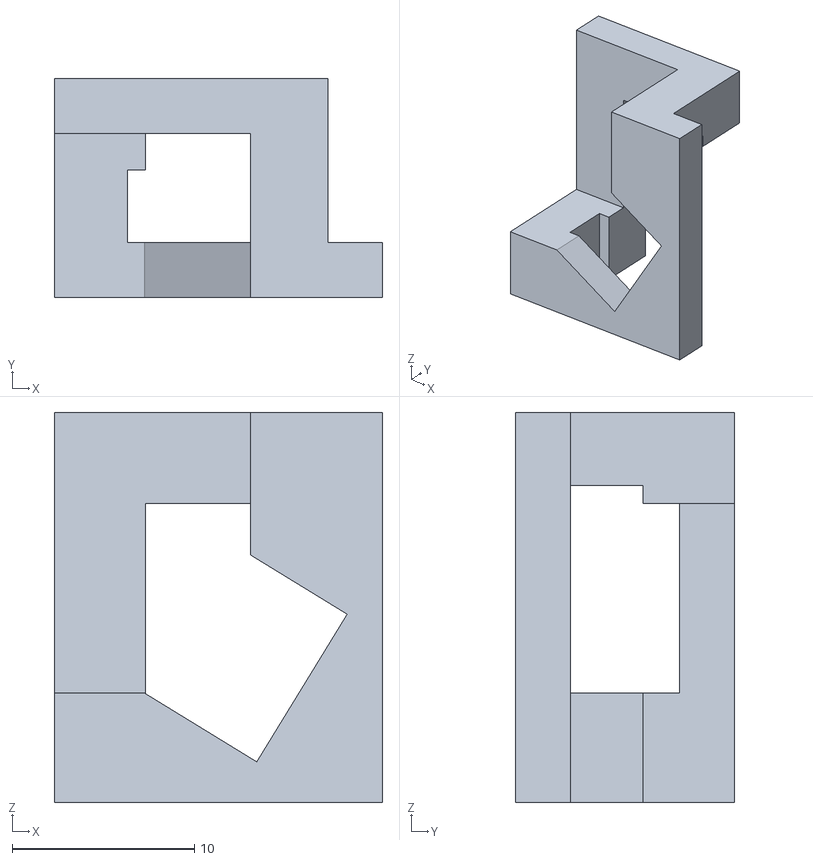
[picture p75: CAD file, 2024-02-02]
hardware/leg/hip/hip-sensor-cap/hip-encoder-shell.stl
18.0 x 12.0 x 21.4
