AnMe3z/quadruped-version-3/hardware/leg/hip/hip-sensor-cap/hip-sensor-cap-Body.stl

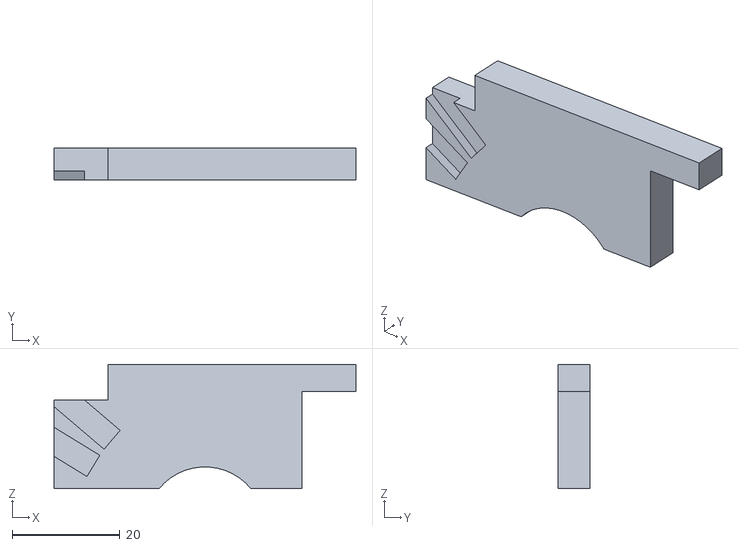
[picture p76: CAD file, 2024-01-21]
hardware/leg/hip/hip-sensor-cap/hip-sensor-cap-Body.stl
56.0 x 6.00 x 23.0
