AnMe3z/quadruped-version-3/hardware/leg/hip/hip-sensor-cap/hip-cap-support.FCStd

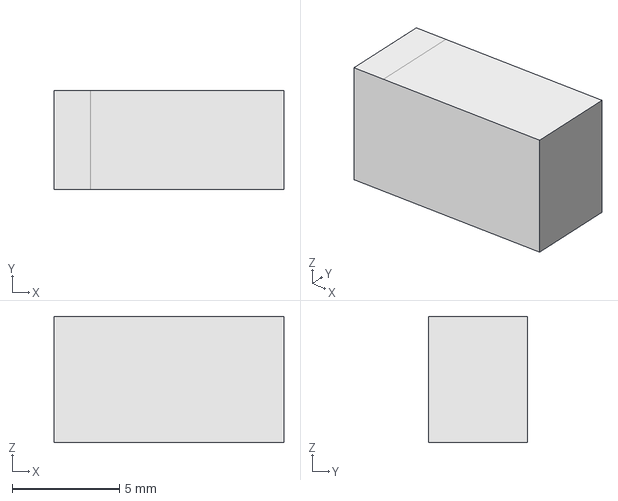
[picture p77: CAD file, 2024-01-02]
hardware/leg/hip/hip-sensor-cap/hip-cap-support.FCStd
10.7 x 4.60 x 5.87 mm
