AnMe3z/quadruped-version-3/hardware/leg/hip/hip-sensor-cap/hip-sensor-cap-224.stl

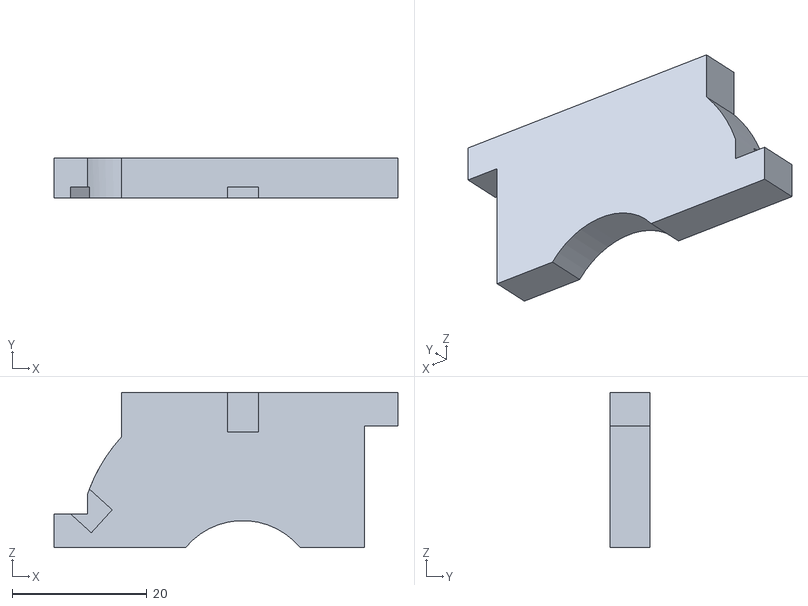
[picture p78: CAD file, 2023-12-26]
hardware/leg/hip/hip-sensor-cap/hip-sensor-cap-224.stl
51.0 x 6.00 x 23.0
