AnMe3z/quadruped-version-3/hardware/schematics/motor-driver/motor-driver.kicad_sch

## KiCad design hardware/schematics/motor-driver/motor-driver.kicad_sch (2023-11-23)

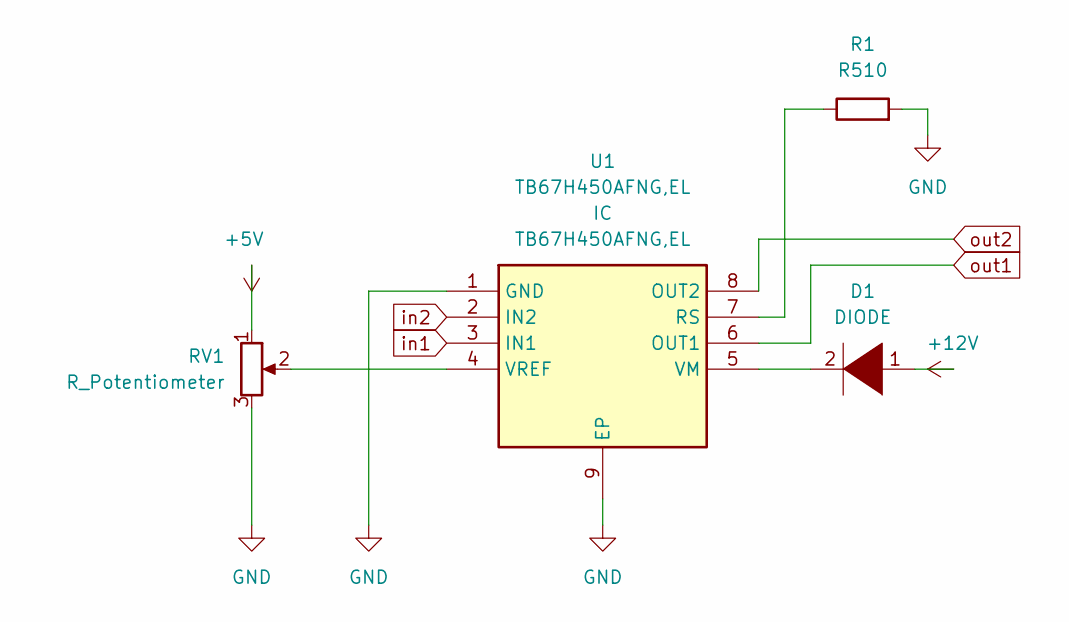
[picture p89: schematic motor-driver.kicad_sch]

Parts:
D1: DIODE
R1: R510
RV1: R_Potentiometer
U1: TB67H450AFNG,EL; Mouser Part Number 757-TB67H450AFNGEL

Connections:
unnamed: D1.2 (A), U1.5 (VM)
unnamed: R1.1, U1.7 (RS)
unnamed: RV1.2, U1.4 (VREF)
in1: U1.3 (IN1)
in2: U1.2 (IN2)
out1: U1.6 (OUT1)
out2: U1.8 (OUT2)
